AndreaFavero71/cubotino_pocket/stp/Structure_pocket.stp

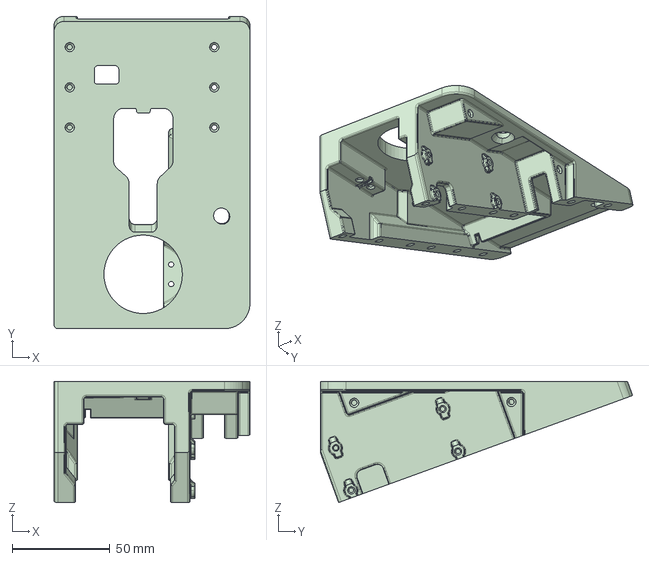
[picture p17: CAD file, 2024-02-11]
stp/Structure_pocket.stp
100.0 x 159.4 x 61.8 mm
