AndreaFavero71/cubotino_pocket/stp/PCB_cover_display_UsbC.stp

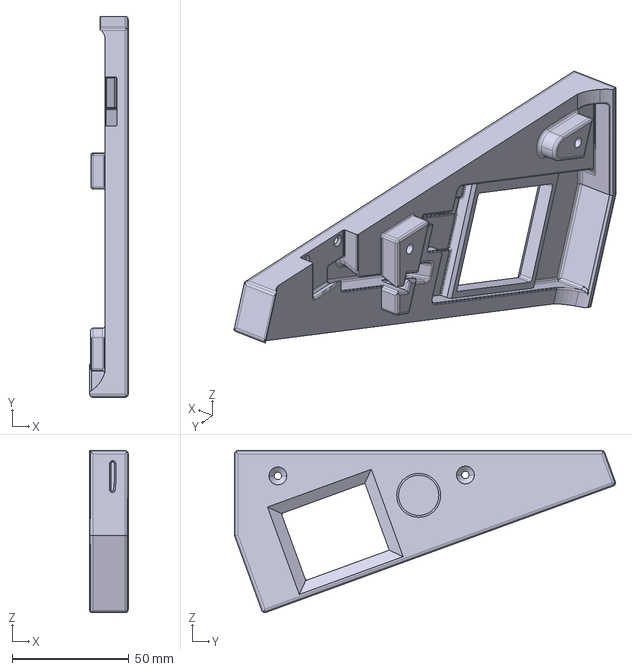
[picture p18: CAD file, 2024-02-11]
stp/PCB_cover_display_UsbC.stp
16.5 x 163.0 x 69.4 mm
