AndreaFavero71/cubotino_pocket/src/Cubotino_P.py

#!/usr/bin/python
# coding: utf-8

"""
#############################################################################################################
#  Andrea Favero, 29 March 2024
#
#  This code relates to CUBOTino 2x2x2 (Pocket), a very small and simple Rubik's cube solver robot 3D printed.
#  CUBOTino_P is the autonomous version of the CUBOTino robot series, for the 2x2x2 Rubik's cube.
#
#  Demo at https: https://youtu.be/wB4MwINGon0
#  Instructions: https://www.instructables.com/CUBOTino-Pocket-Optimal-Solver-Robot-for-Rubiks-Cu/
#
#  This is the core script, that interracts with a few other files.
#  Many functions of this code have been developed on 2021, for my first robot (https://youtu.be/oYRXe4NyJqs).
#
#  The cube status is detected via a camera system (PiCamera) and OpenCV .
#  Kociemba solver is used for the optimal solution (https://github.com/hkociemba/Rubiks2x2x2-OptimalSolver)
#  Credits to Mr. Kociemba for his great job, and helping me to modify the solver for optimal quarter turn.
#  Search for CUBOTino on www.instructables.com, to find more info about this robot family.
#
#  Developped on:
#  - Raspberry Pi Zero2W
#  - Raspberry Pi OS Bulleys, with desktop environment
#
#############################################################################################################
"""


# __version__ variable
version = '2.1 (29 March 2024)'


################  setting argparser for robot remote usage, and other settings  #################
import argparse

# argument parser object creation
parser = argparse.ArgumentParser(description='CLI arguments for Cubotino_P.py')

# --version argument is added to the parser
parser.add_argument("-v", "--version", help='Shows the script version.', action='version',
                    version=f'%(prog)s ver:{version}')

# --debug argument is added to the parser
parser.add_argument("-f", "--twosteps", action='store_true',
                    help="From Flip-Up to close_cover in 2 movements instead of 1")

# --debug argument is added to the parser
parser.add_argument("-d", "--debug", action='store_true',
                    help="Activates printout of settings, variables and info for debug purpose")

# --no_animation argument is added to the parser
parser.add_argument("--no_animation", action='store_true',
                    help="Deactivates the animation on display and screen")

# --cv_wow argument is added to the parser
parser.add_argument("--cv_wow", action='store_true',
                    help="Activates the cv_wow (image analysis steps) on screen")

# --F_deg argument is added to the parser
parser.add_argument("-F", "--F_deg", action='store_true',
                    help="CPU temperature in Fahrenheit degrees")

# --cycles argument is added to the parser
parser.add_argument("-c", "--cycles", type=int, 
                    help="Input the number of automated scrambling and solving cycles")

# --pause argument is added to the parser
parser.add_argument("-p", "--pause", type=int, 
                    help="Input the pause time, in secs, between automated cycles")

# --shutoff argument is added to the parser
parser.add_argument("-s", "--shutoff", action='store_true',
                    help="Shuts the RPI off, after the automated scrambling and solving cycles")

# --timer argument is added to the parser
parser.add_argument("-t", "--timer", action='store_true',
                    help="Timer is visualized after the scrambling function (max 1h)")

# --picamera_test argument is added to the parser
parser.add_argument("--picamera_test", action='store_true',
                    help="Visualizes PiCamera images for test purpose")

# --no_btn argument is added to the parser
parser.add_argument("--no_btn", action='store_true',
                    help="Starts the first solving cycles without using the touch button")

# --silent is added to the parser
parser.add_argument("--silent", action='store_true',
                    help="Deactivate servos, for 'quite' debug of non-servos related aspects")

# --slow_t is added to the parser
parser.add_argument("--slow_t", type=int,
                    help="Input additional resting (integer as tenth of secs) per each servo movement")

args = parser.parse_args()   # argument parsed assignement
# ###############################################################################################


import sys                                               # sys library is imported





def import_parameters(debug=False):
    """ Function to import parameters from a json file.
        It makes easier to list/document/change the variables that are expected to vary on each robot."""
    
    from Cubotino_P_settings_manager import settings as settings  # settings manager Class
    
    global frameless_cube, camera_width_res, camera_hight_res, s_mode
    global expo_shift, kl, x_l, x_r, y_u, y_b, w_f, w_s, square_ratio, rhombus_ratio
    global delta_area_limit, collage_w, marg_coef, cam_led_bright, cam_led_auto
    global detect_timeout, show_time, warn_time, quit_time, cover_self_close, vnc_delay, fcs_delay
    global built_by, built_by_x, built_by_fs

    try:                                                  # tentative
        sett = settings.get_settings()                    # settings are retrieved from the settings Class
        frameless_cube = sett['frameless_cube']           # cube frameless (with/without black frame around the facelets)
        expo_shift = sett['expo_shift']                   # camera exposure shift
        kl = sett['kl']                                   # coefficient for PiCamera stability acceptance (l= lower)
        x_l = sett['x_l']                                 # image crop on left (before warping)
        x_r = sett['x_r']                                 # image crop on right (before warping)
        y_u = sett['y_u']                                 # image crop on top (before warping)
        y_b = sett['y_b']                                 # image crop on bottom (before warping)
        w_f = sett['warp_fraction']                       # coeff for warping the image
        w_s = sett['warp_slicing']                        # coeff for cropping the bottom warped image
        square_ratio = sett['square_ratio']               # acceptance threshold for square sides difference
        rhombus_ratio = sett['rhombus_ratio']             # acceptance threshold for rhombus axes difference
        delta_area_limit = sett['delta_area_limit']       # acceptance threshold for facelet area dev from median
        collage_w = sett['collage_w']                     # image width for unfolded cube collage
        marg_coef = sett['marg_coef']                     # cropping margin arounf faces for immage collage
        cam_led_bright = sett['cam_led_bright']           # PWM level for the 3W led at Top_cover
        detect_timeout = sett['detect_timeout']           # timeout for cube status detection
        show_time = sett['show_time']                     # showing time of the unfolded cube image collage
        warn_time = sett['warn_time']                     # solve button pressing time before get a worning
        quit_time = sett['quit_time']                     # solve button pressing time before the quit process
        vnc_delay = sett['vnc_delay']                     # delay for cube moving to next face at scan (for VNC viewer)
        built_by = sett['built_by']                       # maker's name to add on the Cubotino logo
        built_by_x = sett['built_by_x']                   # x coordinate for maker's name on display
        built_by_fs = sett['built_by_fs']                 # font size for the maker's name on display
        fcs_delay = sett['fcs_delay']                     # delay in secs to switch to Fix Coordinates System for facelets position
        cover_self_close = sett['cover_self_close']       # cover_self_close parameter 
        
        if debug:                                         # case debug variable is set true
            fname = settings.get_settings_fname()         # settings filename is retrieved
            print('\nImporting settings from the text file:', fname)  # feedback is printed to the terminal
            for param, s in sett.items():                 # iteration over the settings dict
                print(f"{param}: {s}")                    # feedback is printed to the terminal
            print()                                       # prints an empty line
        
        return True, sett                                 # return True for loaded settings and the sett dictionary
    
    except:   # exception will be raised if json keys differs, or parameters cannot be converted to int/float
        print('Error at imported_parameters function in Cubotino_P.py')   # feedback is printed to the terminal                                  
        return False, ''                                  # return robot_init_status variable, that is False
    






def import_libraries():
    """ Import of the needed libraries.
        These librries are imported after those needed for the display management.
        Kociemba solver is tentatively imported considering three installation/copy methods."""
    
    global servo, rm, Popen, PIPE, camera, GPIO, median, dt, sv, cubie
    global np, math, time, cv2, os, pathlib
    
    # import custom libraries
    from Cubotino_P_settings_manager import settings as settings   # custom library managing the settings from<>to the settings files
    import Cubotino_P_servos as servo                     # custom library controlling Cubotino servos and led module
    import Cubotino_P_moves as rm                         # custom library, traslates the cuber solution string in robot movements string

    # import non-custom libraries
    from statistics import median                         # median is used as sanity check while evaluating facelets contours
    from subprocess import Popen, PIPE                    # module for interacting with some shell commands
    import os.path, pathlib                               # import libraries for file and folder management
    import RPi.GPIO as GPIO                               # import RPi GPIO library
    import datetime as dt                                 # mainly used as timestamp, like on data logging
    import numpy as np                                    # data array management
    import math                                           # math package
    import time                                           # time package
    import os                                             # os is imported to ensure the file presence check/make
    

    disp.show_on_display('LOADING', 'openCV', fs1=24, fs2=26)  # feedback is printed to the display
    print("Loading solver:")                              # feedback is printed to the terminal
    disp.set_backlight(1)                                 # display backlight is turned on, in case it wasn't
    import cv2                                            # computer vision package
    print(f'CV2 version: {cv2.__version__}')              # print to terminal the cv2 version
    disp.set_backlight(0)                                 # display backlight is turned off
    

    disp.show_on_display('LOADING', 'SOLVER', fs1=24, fs2=27)  # feedback is printed to the display
    print("Loading solver:")                              # feedback is printed to the terminal
    disp.set_backlight(1)                                 # display backlight is turned on, in case it wasn't

    # importing Kociemba solver
    solver_found = False                                  # boolean to track the import the copied solver in subfolder       
    folder = pathlib.Path().resolve()                     # active folder (should be home/pi/cubotino_pocket)  
    fname = os.path.join(folder,'solver2x2x2','solver.py') # active folder + Solver2x2x2 + solver name
    if os.path.exists(fname):                             # case the solver exists in 'Solver2x2x2' subfolder
        try:                                              # attempt
            import solver2x2x2.solver as sv               # import Kociemba solver copied in sub-folder
            import solver2x2x2.cubie as cubie             # import cubie Kociemba solver library part
            solver_found = True                           # boolean to track the  import the copied solver in subfolder
            if debug:                                     # case debug variable is set True            
                print('Found Kociemba solver in solver2x2x2 subfolder')  # feedback is printed to the terminal
        except:                                           # exception is raised if no library in folder or other issues
            solver_found = False                          # boolean to track the import the copied solver in subfolder
    else:
        solver_found = False                              # boolean to track the import the copied solver in subfolder
    
    if not solver_found:                                  # case no one solver has been imported
        print('\nNot found Kociemba solver')              # feedback is printed to the terminal
        disp.show_on_display('NO SOLVER', 'FOUND', fs1=19, fs2=28) # feedback is printed to the display
        time.sleep(5)                                     # delay to let user the time to read the display
        quit_func(quit_script=True)                       # script is quitted







def press_to_start():
    """ Print PRESS TO START to display, and waits until the touch button is pressed to escape the infinite loop"""
    
    global robot_idle
    
    choice = ''                                # variable to store the user choice (solve or scramble)
    robot_idle = True                          # robot is idling
    disp.set_backlight(1)                      # display backlight is turned on, in case it wasn't
    txt1 = 'PRESS TO'                          # text to print at first row
    txt2 = 'START'                             # text to print at second row
    fs_text2 = 32                              # font size at second row
    disp.show_on_display(txt1, txt2, fs2=fs_text2)   # request user to touch the button to start a cycle
    ref_time = time.time()                     # current time is assigned to ref_time variable
    cubotino_logo = False                      # boolean to alternate text with Cubotino logo on display
    display_time = 1                           # time (in sec) for each display page
    while True:                                # infinite loop
        if time.time() - ref_time >= display_time:   # time is checked
            if not cubotino_logo:              # case cubotino logo boolean is false  
                disp.show_cubotino()           # shows the Cubotino logo on the display, for delay time
                ref_time = time.time()         # current time is assigned to ref_time variable
                cubotino_logo = True           # cubotino logo boolean is set true                           
            else:                              # case cubotino logo boolean is false  
                disp.show_on_display(txt1, txt2, fs2=fs_text2)    # request user to touch the button to start a cycle
                ref_time = time.time()         # current time is assigned to ref_time variable
                cubotino_logo = False          # cubotino logo boolean is set false
            time.sleep(0.05)                   # little sleep time 
            
        if GPIO.input(touch_btn):              # case touch_button is 'pressed'
            servo.cam_led_On(cam_led_bright)   # led on top_cover is switched on as button feedback
            choice = solve_or_scramble()       # function for single/double touch (solve or scramble)
            return choice                      # choice is returned, breaking inner and outer while loop


##### addition for Maker Faire setup ##########
# it uses two inputs in logic AND to start the robot. These buttons don't do enything else (no scrambling, no time filtering)
        if GPIO.input(touch_btn1_faire) and GPIO.input(touch_btn2_faire):
            # case both the touch buttons on the faire setup are 'pressed'
            return 'solve'  # 'solve' is returned
###############################################







def solve_or_scramble():
    """ Sense for a single or double touches at the touch sensor, within a time limit.
        Returns 'solve' when single touch and 'scramble' when multiple touches.
        If the button is kept pressed longer, the robot can be restarted or shutted OFF."""
    
    global robot_idle, side
    
    choice = ''                               # variable to store the user choice (solve or scramble)
    state = False                             # boolean state to check flank is set false, 
    max_delay = 0.8                           # max time between touches, to decide if single or multi touches
    extra_time = 1.2                          # extra time to accept a single button press as intention to 'solve' a cube
    last_time = time.time()                   # variable holding the time of the last change to 'pressed' button
    pulse_count = 0                           # pulses counter is initially set to zero
    
    while robot_idle:                         # boolean robot_idle is used to sustain this loop
        new_state = GPIO.input(touch_btn)     # touch button status is assigned (it's ON when pressed)
        if new_state and not state:           # case the touch sensor changes from 'not pressed' to 'pressed'
            pulse_count += 1                  # pulse counter is incremented
            state = True                      # set the state to true
            last_time = time.time()           # updtaes the variable that hold
        elif not new_state:                   # case the touch sensor is 'not pressed'
            state = False                     # state is changed to false
        
        # case the elapsed time is bigger than max time and at least 1 pulse
        if time.time() > (last_time + max_delay) and pulse_count > 0:
            if GPIO.input(touch_btn):         # case button is still pressed
                if pulse_count == 1:          # case the button has been pressed only once
                    if time.time()< last_time + max_delay + extra_time: # case time is within the given extratime
                        servo.cam_led_Off()   # led OFF at Top_cover, to suggest the user to remove the finger
                        choice = 'solve'      # 'solve' is assigned to choice variable
                    else:                     # case elapsed time is more than extra_time
                        servo.cam_led_Off()   # led OFF at Top_cover
                        break                 # while loop is interrupted
                elif pulse_count > 1:         # case the button has been pressed multiple times
                    servo.cam_led_Off()       # led OFF at Top_cover
                    break                     # while loop is interrupted

            elif not GPIO.input(touch_btn):   # touch button is NOT pressed
                if pulse_count == 1:          # case pulses equal one, and button not 'pressed'
                    choice = 'solve'          # 'solve' is assigned to choice variable
                elif pulse_count >= 2:        # case pulses are two or more,  and button not 'pressed'
                    servo.cam_led_Off()       # led OFF at Top_cover when scrambling is chosen
                    choice = 'scramble'       # 'scramble' is assigned to choice variable
                else:                         # other cases (button kept pressed long without a release within maxtime)
                    pulse_count = 0           # pulse counter is reset to zero
                    choice = ''               # empty string is assigned to choice variable
                return choice                 # choice is returned
    
    servo.cam_led_Off()    # led OFF at Top_cover when scrambling is chosen
    robot_idle = False     # robot_idle is set false
    stop_or_quit()         # stop or quit function is called, when the while loop is interrupted
    choice = ''            # empty string is assigned to choice variable
    return choice          # choice is returned







def check_screen_presence():
    """ Checks if a display is connected, eventually via VNC; This is not the little display (SPI) ...."""
    
    import os
    
    if 'DISPLAY' in os.environ:                # case the environment variable DISPLAY is set to 1 (there is a display)
        return True                            # function returns true, meaning there is a screen connected
    else:                                      # case the environment variable DISPLAY is set to 0 (there is NOT a display)
        return False                           # function returns false, meaning there is NOT a screen connected







def get_os_version():
    """Returns the Raspberry Pi OS (in digits)."""
    os_version = 0
    with open('/etc/os-release', 'r') as file:
        for row in file:
            if "VERSION_ID" in row:
                os_version = int(''.join(x for x in row if x.isdigit()))
                return os_version
    return os_version







def set_camera(expo_shift=0):
    """ Set the camera and its resolution.
        Different libraries will be used depending on OS version (picamera on OS 10, picamera2 on OS 11)"""
  
    os_version = get_os_version()
    
    if os_version >0 and os_version <= 10:
        from Cubotino_P_camera_os10 import camera
        width = camera.get_width()
        height = camera.get_height()
        
        # case cube side is zero, no request to stop the robot and not automated cycles
        if side == 0 and not robot_stop and cycles_num == 0 and not picamera_test:
            camera.printout()
        
    elif os_version >= 11:
        from Cubotino_P_camera_os11 import camera
        width = camera.get_width()
        height = camera.get_height()
        time.sleep(1)
        camera.set_exposure_shift(expo_shift)
    
    else:
        print("Raspberry Pi OS version not recognized")
    
    return camera, width, height







def robot_camera_setting(debug, os_version, camera):
    """ According to PiCamera documentation it is required a couple of seconds to warmup the camera.
    If the robot start-button is pressed right after placing the cube, the camera has to update the gains previously set,
    that means from when the camera was pointing the black cube support; this can take up to 20 secs to get all
    the gains stable (awb gains are rather slow to update).
    Much different is when the cube is on the cube support for few secs when the button is pressed.
    To properly cover all the possible situations, this fuction releases the camera warm-up phase only after
    all the gains are stable. This function returns the camera parameters once within absolute variation < 5% from
    the average of 'pts' points."""
    
    stable_camera = False           # flag to trak whether the camera gets stable within the timeout
    
    ku = 2-kl                       # Upper koefficient to define acceptance bandwidth (105%)
    
    if os_version <= 10:            # case the OS is Buster or older
        t_max = 5                   # timeout to quit this function and deliver the latest camera parameters
        if debug:                   # case debug variable is set True
            pts = 8                 # consecutive datapoints to analyse if parameters within acceptable range
        else:                       # case debug variable is set False
            pts = 10                # consecutive datapoints to analyse if parameters within acceptable range
        
    elif os_version >= 11:          # case the OS is Bullseye or newer
        t_max = 3                   # timeout to quit this function and deliver the latest camera parameter
        if debug:                   # case debug variable is set True
            pts = 9                 # consecutive datapoints to analyse if parameters within acceptable range
        else:                       # case debug variable is set False
            pts = 11                # consecutive datapoints to analyse if parameters within acceptable range
    
    if Rpi_ZeroW:                   # case a ZeroW board is used
        t_max = 3*t_max             # max time for camera setting is increased
    
    a_gain_list=[]                  # list to store the Picamera analog gain, during pre-scan period
    d_gain_list=[]                  # list to store the Picamera digital gain, during pre-scan period
    awb_blue_list=[]                # list to store the Picamera AWB gain, for blue, during pre-scan period
    awb_red_list=[]                 # list to store the Picamera AWB gain, for red, during pre-scan period
    exp_list=[]                     # list to store the Picamera exposure time, during pre-scan period
    PiCamera_param=()               # empty tuple is assigned to PiCamera_param variable
    
    if screen and not robot_stop:                      # case screen variable is set True
        if fixWindPos:                                 # case the fixWindPos variable is chosen
            cv2.namedWindow('cube')                    # create the cube window
            cv2.moveWindow('cube', 0,0)                # move the window to (0,0)

    t_start = time.time()                              # time reference
    while time.time()-t_start<t_max:                   # timeout for camera stabilization
        if screen and not robot_stop:                  # case screen variable is set True
            frame, w, h = read_camera()                # camera reading, not necessary but nice to show
            cv2.imshow('cube', frame)                  # shows the frame 
            cv2.waitKey(1)                             # tot refresh time of 1ms (in reality much more)
        else:                                          # case screen variable is set False
            time.sleep(0.11)                           # similar time when there is no camera reading and plot to screen
        
        if os_version <= 10:                           # case the flashed OS is 10 (Buster) or older
            metadata = camera.get_data()               # camera is inquire
        elif os_version >= 11:                         # case the flashed OS is 11 (Bullseye) or newer
            metadata = camera.get_metadata()           # camera is inquired
        
        a_gain = metadata["AnalogueGain"]              # analog gain from metadata is assigned to the variable
        d_gain = metadata["DigitalGain"]               # digital gain from metadata is assigned to the variable
        awb_gains = metadata["ColourGains"]            # AWB gains from metadata is assigned to the variable
        exposure = metadata["ExposureTime"]            # exposure time from metadata is assigned to the variable        
        
        a_gain_list.append(float(a_gain))              # analog gain is appended to a list
        d_gain_list.append(float(d_gain))              # digital gain is appended to a list
        awb_blue_list.append(float(awb_gains[0]))      # awb blue part gain is appended to a list
        awb_red_list.append(float(awb_gains[1]))       # awb blue part gain is appended to a list
        exp_list.append(exposure)                      # exposure time (micro secs) is appended to a list

        a_check=False                                  # a flag is negatively set for analog gain (being stable...)
        d_check=False                                  # a flag is negatively set for digital gain (being stable...)
        awb_blue_check=False                           # a flag is negatively set for awb blue gain (being stable...)
        awb_red_check=False                            # a flag is negatively set for awb red gain (being stable...)
        exp_check=False                                # a flag is negatively set for the exposure time (being stable...)

        if len(a_gain_list) > pts:                     # requested a minimum amount of datapoints
            check = a_gain_list[-1]/(sum(a_gain_list[-pts:])/pts)  # last analog gain value is compared to the average of last pts points
            if check > kl and check < ku:              # if comparison within acceptance boundaries
                a_check=True                           # flag is positively set for this gain             
        
            check = awb_blue_list[-1]/(sum(awb_blue_list[-pts:])/pts) # last awb_blue gain is compared to the average of last pts points
            if check > kl and check < ku:              # if comparison within acceptance boundaries
                awb_blue_check=True                    # flag is positively set for this gain    
                
            check = awb_red_list[-1]/(sum(awb_red_list[-pts:])/pts) # last awb_red gain is compared to the average of last pts points
            if check > kl and check < ku:              # if comparison within acceptance boundarie
                awb_red_check=True                     # flag is positively set for this gain
            
            check = exp_list[-1]/(sum(exp_list[-pts:])/pts)  # last exposure time is compared to the average of last pts points
            if check > kl and check < ku:              # if comparison within acceptance boundarie
                exp_check=True                         # flag is positively set for the exposure time                
     
            if a_check and awb_blue_check and awb_red_check and exp_check: # if all gains are stable
                stable_camera = True
                break                                  # camera warmup while loop break
     
    if len(a_gain_list)==0:                            # case a_gain_list (the first list of camera setting) is empty
        print("The camera takes very long time to stabilize")  # feedback is printed to terminal
        print("The script is ended")                   # feedback is printed to terminal
        quit_func(quit_script=True)                    # script is quitted
    else:                                              # case the first list (a_gain_list) is not empty
        a_gain_value = a_gain_list[-1]                 # last a_gain list value is assigned
        d_gain_value = d_gain_list[-1]                 # last d_gain list value is assigned
        awb_gains = (awb_blue_list[-1], awb_red_list[-1])  # last awb_gains list tuple is assigned
        exposure = exp_list[-1]                        # last exposure list value is assigned
    
    # latest PiCamera settings, in auto mode, are assigned to a tuple
    PiCamera_param=(a_gain_value, d_gain_value, awb_gains, exposure, stable_camera)  
    
    t_stable = round(time.time()-t_start,1)            # time to get the camera stable on this cube face
    
    if debug:                                          # case debug is set True
        print('\nPiCamera warmup function:')           # feedback is printed to the terminal
        print('analog_gain_list',a_gain_list)          # feedback is printed to the terminal
        print('digital_gain_list',d_gain_list)         # feedback is printed to the terminal
        print('awb_blue_list',awb_blue_list)           # feedback is printed to the terminal
        print('awb_red_list',awb_red_list)             # feedback is printed to the terminal
        print('camera exp_list', exp_list)             # feedback is printed to the terminal
        print('datapoints:', len(exp_list))            # feedback is printed to the terminal
        print(f'PiCamera: AWB and Exposure being stable in {t_stable} secs')  # feedback is printed to the terminal
    
    return PiCamera_param                              # tuple with the camera stable parameter is returned







def robot_consistent_camera_images(debug, os_version, camera, start_time):
    """ Picamera is left in set in Auto mode for Exposure and AWB gains, while presenting 4 cube faces.
    These parameters are retrieved from PiCamera after showing each of these first 4 cube faces.
    Picamera is then set to Manual mode by setting the average exposure time and average AWB to the camera.
    This approach prevents the PiCamera to keep adjusting the AWB and Exposure while reading the different cube faces.
    The average values set to the camera mitigates large differences at the cube, i.e. when the cube is already solved."""
    
    if robot_stop:            # case the robot has been requested to stop
        return                # function is terminated
    
    disp.show_on_display('SETTING', 'CAMERA', fs1=23, fs2=21)    # feedback is printed to the display
    
    
    if os_version <= 10:
        awb_mode = 0          # this is the AUTO mode fro the AWB, and it works well with Cubotino
    
    elif os_version >= 11:
        # AWB mode (AutoWitheBalance) to use when the camera is set to automati mode
        # AwbMode: 0=Auto - any illumant, 1=Tungsten - tungsten lighting, 2=Fluorescent - fluorescent lighting
        # 3=Indoor - indoor illumination, 4=Daylight - daylight illumination, 5=Cloudy - cloudy illumination
        awb_mode = 3          # this is the  mode that seems to work better in Cubotino
    
    camera.set_auto(debug, awb_mode, expo_shift)        # camera is set to automatic mode, by also passing the chosen AWB mode
    
    if debug:                                           # case debug variable is set True
        print("\nCamera settings (in Auto mode):")      # feedback is printed to the terminal
        print('\nPiCamera: Reading the stable camera parameters on four cube sides')  # feedback is printed to the terminal

    a_gain_list=[]                                      # list to store the Picamera analog gain, during pre-scan period
    d_gain_list=[]                                      # list to store the Picamera digital gain, during pre-scan period
    awb_blue_list=[]                                    # list to store the Picamera AWB gain, for blue, during pre-scan period
    awb_red_list=[]                                     # list to store the Picamera AWB gain, for red, during pre-scan period
    exp_list=[]                                         # list to store the Picamera exposure time, during pre-scan period
    stable_camera_list=[]                               # list to store the Picamera stability reach within timeout

    # PiCamera is inquired on 4 cube sides reachable via a simple cube flip, to later fix an average parameters
    for i in (1,2,3,4):                                 # iterate over 4 faces reachable via a single cube flip    
        if i > 1:                                       # case i (face) is not the first
            robot_to_cube_side(1,cam_led_bright)        # flipping the cube, to reach the next side 

        PiCamera_param = robot_camera_setting(debug, os_version, camera)  # camera parameter are returned
        a_gain_list.append(PiCamera_param[0])           # analog gain is added to a_gain_list
        d_gain_list.append(PiCamera_param[1])           # digital gain is added to d_gain_list
        awb_blue_list.append(PiCamera_param[2][0])      # awb blue is added to awb_blue_list
        awb_red_list.append(PiCamera_param[2][1])       # awb red is added to awb_red_list
        exp_list.append(PiCamera_param[3])              # exposure time is added to exp_list
        stable_camera_list.append(PiCamera_param[4])    # boolean stable_camera is added to stable_camera_list
        
        if debug:                                       # case debug variable is set True
            print(f"\nCamera settings (in Auto mode) at face {i}:")  # feedback is printed to the terminal
            print(PiCamera_param)                       # feedback is printed to the terminal
            print()                                     # print an empty line
            if i == 4:                                  # case i (face) equals four
                print("\n"*3)                           # prints 3 empty lines
    
    # setting the camera in manual mode, for consistent images when scanning
    a_gain = float(sum(a_gain_list)/len(a_gain_list))   # average a_gain is calculated and assigned
    d_gain = float(sum(d_gain_list)/len(d_gain_list))   # average d_gain is calculated and assigned
    awb_gains = (float(sum(awb_blue_list)/len(awb_blue_list)), float(sum(awb_red_list)/len(awb_red_list)))  # average awb_gains is calculated and assigned
    shutter_time = int(sum(exp_list)/len(exp_list))     # average exposure time of UBDF faces
    
    camera.set_gains(debug, a_gain, d_gain, awb_gains)  # sets the gains to the PiCamera, for consisent images
    camera.set_exposure(shutter_time)                   # sets the shutter time to the PiCamera, for consistent images
    
    t_ref = time.time()                                 # current time is assigned to a reference variable
    while time.time()-t_ref < 2:                        # while loop for max 2 seconds
        exposure = camera.get_exposure()                # read picamera exposure time (microsec)
        if abs(exposure-shutter_time) < 0.10*shutter_time:  # case the camera shutter time deviates less than 10% from target shutter_time
            break                                       # while loop is interrupted       
    
    if screen:                                          # case there is a screen connected
        print(f'Camera setting: Fixed gains and shutter time for cube  scanning, in {round(time.time()-start_time,1)} secs')# feedback is printed to the terminal
    
    if debug:                                           # case debug variable is set True
        print('\n\nExposure time on UBDF faces : ', exp_list)  # feedback is printed to the terminal
        print('Average exposure time: ', int(sum(exp_list)/len(exp_list)), 'micro secs') # feedback is printed to the terminal
        print('Shutter_time set by PiCamera: ', camera.get_exposure(), ' micro secs')  # feedback is printed to the terminal
        print('Camera stable within timeout', stable_camera_list)   # feedback is printed to the terminal
        print('\nPiCamera parameters, for consistent images, are set to:')  # feedback is printed to the terminal
        print('Analog_gain_list',a_gain_list)           # feedback is printed to the terminal
        print('Digital_gain_list',d_gain_list)          # feedback is printed to the terminal
        print('Awb_blue_list',awb_blue_list)            # feedback is printed to the terminal
        print('Awb_red_list',awb_red_list)              # feedback is printed to the terminal
        print("\n"*4)                                   # prints four empty lines

    disp.clean_display()                                # cleans the display
    robot_to_cube_side(1,cam_led_bright)                # flipping the cube, to reach the 1st face for the scanning process







def read_camera():
    """ Returns the camera reading, and dimensions."""
    
    global previous_time
    
    frame = camera.get_frame()                                    # single frame array request to camera Class
    width = camera.get_width()                                    # camera width request to camera Class
    height = camera.get_height()                                  # camera height request to camera Class
    
    if len(frame)==0:                                             # case the frame is empty
        print('camera frame not available')                       # feedback is print to the terminal
    
    else:                                                         # case the frame is not empty
        if not picamera_test:                                     # case picamera_test is false
            frame, w, h = frame_cropping(frame, width, height, x_l, x_r, y_u, y_b)  # frame is cropped in order to limit the image area to analyze
            frame, w, h = warp_image(frame, w, h, w_f, w_s)       # frame is warped to have a top like view toward the top cube face
            scale = 0.75 if cv_wow else 0.8                       # scaling factor according to cv_wow i 
            frame, w, h = frame_resize(frame, w, h, scale=scale)  # frame is resized (to smaller size), to gain some speed
        
        elif picamera_test:                                       # case picamera_test is True (also when servos_GUI script is used):
            w = width                                             # widht is assigned to w
            h = height                                            # height is assigned to h
        
        return frame, w, h







def frame_cropping(frame, width, height, x_l, x_r, y_u, y_b):
    """Frame cropping, to prevent reading the back cube side and to increase overal speed.
    Due to short camera distance from the cube, all the PiCamera sensor area is used,
    therefore pixels reduction is beneficial ro reduce overall memory load.
    For proper setting of these parameters, it is convenient to temporary skip the frame_warping:
    uncomment first row at frame_warping function."""
    
#     uncomment below row (return frame, width, height) to prevent the image cropping
#     this is useful for initial camera positioning (angle) on the top_cover
#     return frame, width, height
    
    frame = frame[y_u: height-y_b , x_l: width-x_r]   # frame is sliced
    w = width - x_l - x_r                             # sliced frame width
    h = height - y_u - y_b                            # sliced frame height
    
    return frame, w, h







def warp_image(frame, w, h, w_f, w_s):
    """ Warp the image to remove perspective and simulate a top like view.
    This because PiCamera is at an angle with reference to the top cube face.
    This allows to analyse the facelets contours (square like, area, etc) in a more precise way.
    This also allows a much nicer cube faces collage."""
    
#     NOTE: uncomment below row to remove the image warping, useful for initial setting the camera frame cropping (frame_cropping)
#     return frame, w, h
    
    if cv_wow:                        # case the cv image analysis plot is set true
        global pre_warp, after_warp   # global variable for the frame content, before and after warping
        pre_warp = frame              # frame is assigned to the pre_warp variable
        ww = w                        # frame width before warping is assigned to a local variable
        hh = h                        # frame height before warping is assigned to a local variable
    
    grid_vertices = np.float32([[0,0], [h,0], [h,w], [0,w]])  # original frame vertices

    d_x = int(w/w_f)            # pixels to 'remove' on top left and top righ sides of frame, to warp the image
    straight = 1+d_x/h          # corrects the cube face deformation 

    warped_vertices = np.float32([[d_x,0], [h,0], [int(straight*h),w], [-d_x, w]])  # frame coordinates for the transformation matrix
    matrix = cv2.getPerspectiveTransform(warped_vertices, grid_vertices)            # compute perspective matrix

    # do perspective transformation, by adding black pixels where needed
    frame = cv2.warpPerspective(frame, matrix, (max(w,h), max(w,h)), cv2.INTER_LINEAR, cv2.BORDER_CONSTANT, borderValue=(0,0,0))
    
    frame = frame[: -d_x, :-int(d_x/w_s)]   # frame slicing to remove part of the added (black) pixels on the right frame side 
    h, w = frame.shape[:2]                  # new frame height and width
    
    if cv_wow:                                           # case the cv image analysis plot is set true
        pre_warp, _, _ = frame_resize(pre_warp, ww, hh)  # re-sized frame is assigned to the pre_warp global variable
        after_warp, _, _ = frame_resize(frame, w, h)     # re-sized frame is assigned to the after_warp global variable
    
    return frame, w, h







def frame_resize(frame_w, ww, hh, scale=0.8):        
    """ Re-sizes the image after the cropping and warping steps, by a scaling factor.
    This is useful to lower the amount of handled data for the facelects and color detection."""
    
    ww = int(ww * scale)                  # new frame width
    hh = int(hh * scale)                  # new frame height
    
    if Rpi_ZeroW:                         # case Rpi_ZeroW is True (armv6 processor)
        interp_method = cv2.INTER_LINEAR  # bilinear interpolation method (prevents crashing with armv6 processor))
    else:                                 # case Rpi_ZeroW is False (not an armv6 processor)
        interp_method = cv2.INTER_AREA    # interpolation method resamples using pizel area relation

    frame_s = cv2.resize(frame_w, (ww, hh), interpolation = interp_method)  # resized frame
    return frame_s, ww, hh







def edge_analysis(frame, w, h):
    """ Image analysis that returns a black & white image, based on the colors borders.
        Different analysis for cube with /withouth the black frame around the facelets."""
    
    if cv_wow and screen:                                    # case screen and cv_wow variables are set true on __main__
        global gray, blurred, canny, dilated, eroded         # images are set as global variable

    gray = cv2.cvtColor(frame, cv2.COLOR_BGR2GRAY)           # from BGR color space to gray scale
    
    if frameless_cube == 'false':                            # case the cube has black frame around the facelets
        blurred = cv2.GaussianBlur(gray, (5, 5), 0)          # low pass gaussian filter, with a 5x5 gaussian filter
        canny = cv2.Canny(blurred, 10, 30)                   # single pixel edges, with intensity gradient range 10 to 30
        kernel = np.ones((5,5), np.uint8)                    # kernel of 5x5 pixels for the dilate transformation
        dilated = cv2.dilate(canny, kernel, iterations = 4)  # higher "iterations" is overall faster
        kernel = np.ones((3,3), np.uint8)                    # smaller kernel is used for the erosion
        eroded = cv2.erode(dilated, kernel, iterations = 2)  # smaller "iterations" keeps the contour apart from the edges
    
    elif frameless_cube == 'true':                           # case the cube is a frameless cube
        blurred = cv2.bilateralFilter(gray, 3, 80, 80)       # low pass bilateral filter, to de-noise while safegarding edges
        canny = cv2.Canny(blurred, 4, 25)                    # single pixel edges, with intensity gradient range 4 to 25
        kernel = np.ones((7,7), np.uint8)                    # kernel of 7x7 pixels for the dilate transformation
        dilated = cv2.dilate(canny, kernel, iterations = 4)  # higher "iterations" is overall faster
        kernel = np.ones((5,5), np.uint8)                    # smaller kernel is used for the erosion
        eroded = cv2.erode(dilated, kernel, iterations = 1)  # smaller "iterations" keeps the contour apart from the edges
    
    # note: when frameless_cube == 'auto' the cube detection takes slightly longer
    elif frameless_cube == 'auto':                           # case for cubes with and without the black frame around the facelets
        blurred = cv2.GaussianBlur(gray, (5, 5), 0)          # low pass gaussian filter, with a 5x5 gaussian filter
        canny_01 = cv2.Canny(blurred, 10, 30)                # single pixel edges, with intensity gradient range 10 to 30
        blurred = cv2.bilateralFilter(gray,4, 200, 200)      # low pass bilateral filter, to de-noise while safegarding edges
        canny_02 = cv2.Canny(blurred, 4, 25)                 # single pixel edges, with intensity gradient range 4 to 25
        canny = cv2.bitwise_or(canny_01, canny_02, mask = None) # canny image, by (OR) combining those generated with parameters with and without frames
        kernel = np.ones((7,7), np.uint8)                    # kernel of 7x7 pixels for the dilate transformation
        dilated = cv2.dilate(canny, kernel, iterations = 3)  # higher "iterations" is overall faster
        kernel = np.ones((3,3), np.uint8)                    # smaller kernel is used for the erosion
        eroded = cv2.erode(dilated, kernel, iterations = 2)  # smaller "iterations" keeps the contour apart from the edges
    
############ visual check edge detection #############
#     cv2.imshow("Gray", gray)           # gray is shown, on a window called Gray
#     cv2.imshow("blurred", blurred)     # blurred is shown, on a window called Blurred
#     cv2.imshow("Canny", canny)         # canny is shown, on a window called Canny
#     cv2.imshow("Dilated", dilated)     # dilated is shown, on a window called Dilated
#     cv2.imshow("Eroded", eroded)       # eroded is shown, on a window called Eroded
######################################################
    
    return eroded, w, h







def show_cv_wow(cube, time=2000):
    """ shows how the image from the camera is altered to detect the facelets.
        Also possible to set a boolean to save those images."""
    
    gap_w = 80       # horizontal gap (width) for all windows from 'Pre_warp' window
    gap_h = 100      # vertical gap (height), above first row of images and between the two rows of windows
    
    # note: for precise window position, after windows name at cv2.namedWindow, the parameter cv2.WINDOW_NORMAL  
    # should be used instead of the cv2.WINDOW_RESIZE (default), but image quality on screen changes too much....
    cv2.namedWindow('Pre_warp')                      # create the Pre_warp window
    cv2.moveWindow('Pre_warp', w, gap_h)             # move the Pre_warp window to coordinate
    cv2.namedWindow('After_warp')                    # create the Frame window
    cv2.moveWindow('After_warp', 2*w+gap_w, gap_h)   # move the Frame window to coordinate
    cv2.namedWindow('Gray')                          # create the Gray window
    cv2.moveWindow('Gray', 3*w+gap_w, gap_h)         # move the Gray window to coordinate
    cv2.namedWindow('blurred')                       # create the Blurred window
    cv2.moveWindow('blurred', 4*w+gap_w, gap_h)      # move the Blurred window to coordinate
    cv2.namedWindow('Canny')                         # create the Canny window
    cv2.moveWindow('Canny', w+gap_w, h+2*gap_h)      # move the Canny window to coordinate
    cv2.namedWindow('Dilated')                       # create the Dilated window
    cv2.moveWindow('Dilated', 2*w+gap_w, h+2*gap_h)  # move the Dilated window to coordinate
    cv2.namedWindow('Eroded')                        # create the Eroded window
    cv2.moveWindow('Eroded', 3*w+gap_w, h+2*gap_h)   # move the Eroded window to coordinate
    cv2.namedWindow('Cube')                          # create the Cube window
    cv2.moveWindow('Cube', 4*w+gap_w, h+2*gap_h)     # move the Cube window to coordinate
    
    cv2.imshow("Pre_warp", pre_warp)                 # pre-warp is shown, on a window called Pre_warp
    cv2.imshow("After_warp", after_warp)             # after_warp is shown, on a window called After_warp
    cv2.imshow("Gray", gray)                         # gray is shown, on a window called Gray
    cv2.imshow("blurred", blurred)                   # blurred is shown, on a window called Blurred
    cv2.imshow("Canny", canny)                       # canny is shown, on a window called Canny
    cv2.imshow("Dilated", dilated)                   # dilated is shown, on a window called Dilated
    cv2.imshow("Eroded", eroded)                     # eroded is shown, on a window called Eroded
    cv2.imshow("Cube", cube)                         # cube is shown, on a window called Cube
    
    if side == 1:                   # case the first cube side is under analysis 
        cv2.waitKey(time + 4000)    # all the openCV windows are showed, with an extra time on first cube side
    else:                           # case the cube side under analysis is not the first side
        cv2.waitKey(time)           # all the openCV windows are showed
    
    save_images = False                                         # boolean to enable/disable saving cv_wow images
    folder = pathlib.Path().resolve()                           # active folder (should be home/pi/cubotino_pocket)  
    if save_images:                                             # case the save_image is True
        folder = os.path.join(folder,'cv_wow_pictures')         # folder to store the cv_wow pictures
        if not os.path.exists(folder):                          # if case the folder does not exist
            os.makedirs(folder)                                 # folder is made if it doesn't exist
        datetime = dt.datetime.now().strftime('%Y%m%d_%H%M%S')  # date_time variable is assigned, for file name
        for i, image in enumerate(('Pre_warp', 'After_warp', 'Gray', 'Blurred', 'Canny', 'Dilated', 'Eroded', 'Cube')):
            if side == 1 and i == 0:                                       # case for first image to save
                print('\n\n##########################################')    # feedback is printed to the terminal
                print('###   saving 48 cv_wow pictures  !!!  ####')        # feedback is printed to the terminal
                print('##########################################\n\n')    # feedback is printed to the terminal
            fname = datetime + '_Side'+ str(side) + '_' + str(i) + '_'+ image + '.png'  # filename constructor
            fname = os.path.join(folder, fname)         # folder+filename for the cube data
            if image == 'Pre_warp':                     # case the image equals to Pre_warp
                cv2.imwrite(fname, pre_warp)            # pre_warp image is saved
            elif image == 'After_warp':                 # case the image equals to Frame
                cv2.imwrite(fname, after_warp)          # frameimage is saved
            elif image == 'Gray':                       # case the image equals to Gray
                cv2.imwrite(fname, gray)                # gray image is saved
            elif image == 'Blurred':                    # case the image equals to Blurred
                cv2.imwrite(fname, blurred)             # blurred image is saved
            elif image == 'Canny':                      # case the image equals to Canny
                cv2.imwrite(fname, canny)               # canny image is saved
            elif image == 'Dilated':                    # case the image equals to Dilated
                cv2.imwrite(fname, dilated)             # dilated image is saved
            elif image == 'Eroded':                     # case the image equals to Eroded
                cv2.imwrite(fname, eroded)              # eroded image is saved
            elif image == 'Cube':                       # case the image equals to Cube
                cv2.imwrite(fname, cube)                # cube image is saved
            else:                                       # case the does not match proposed strings
                print('Error in image list')            # feedback is printed to the terminal







def square_check(data):  
    """Sanity check if a contour has a square like shape; Argument is a contour.
    Calculates quadrilateral's edge delta lenght: [(max edge - min edge)/average of sides length]
    Calculates the ratio between the 2 diagonals (rhonbus axes): min diagonal / max diagonal
    These parameter are later used to verify if the contour can be considered like a square.
    A perfect square will have edge_delta==0 and axes_delta==1."""
    
    edges=[]                    # list of the 4 edges of the quadrilateral
    axes=[]                     # List of axes of symmetry length of the rhombus
    for i in range(len(data)):  # iteration over the contour vertices 
        j = i + 1               # following vertex
        if i==3:                # case the current iteration is on vertex 
            j=0                 # following vertex is set as the first one
        edges.append(math.sqrt((data[j][0]-data[i][0])**2 + (data[j][1]-data[i][1])**2))  # list of the 4 edge's length
        edge_delta = (max(edges)-min(edges))*4/sum(edges)                                 # max side delta over the mean
    
    for i in range(2):          # iteration over 2 (diagonals)
        j = i + 2               # following vertices is the after the next 
        axes.append(math.sqrt((data[j][0]-data[i][0])**2 + (data[j][1]-data[i][1])**2))  # list of the 2 rhobus axes
        axes_delta = min(axes)/max(axes)    # axes delta is the division of the smallest over the largest
    
    return edge_delta, axes_delta







def distance_deviation(data, delta=0.3):
    """ Checks whether the distances between the 4 contours centers are within a pre-defined deviation from the median
    This is a sanity check if all the 4 facelets are compatible with a 2x2 square array shape.
    Aim of this funtion is to exclude contours generated outside the cube, on eventual square like shapes
    detected by the camera at the cube background.
    The approach checks the 2 horizontal distances from the contours center, and the 2 vertical ones.
    Considering the cube can have a certain tilting angle (inclination), Pitagora theorem is used.
    Function returns a list with the index of the countours (exceding the threshold) to be removed from the
    list of contours considered being potential facelets.
    ---------
    | 0 | 1 |
    ---------
    | 2 | 3 | 
    ---------  
    """
    
    d_to_exclude = []        # list of the contour index to be removed, due to excess of distance deviation
    distance_list = []       # list of the horizontal and vertical distance, of each contour from the median
    
    points_h=[1,3]           # coordinates, defining a segment with a previous coordinate,for 2 'horizontal' distances
    for i in points_h:       # iteration over the 6 coordinates
        j=i-1                # the other coordinate used for the segment length
        # horizontal distance between the contours centers
        dist=math.sqrt((data[i]['cx']-data[j]['cx'])**2 + (data[i]['cy']-data[j]['cy'])**2)
        distance_list.append(dist)  # list with horizontal distance between the contours centers

    points_v=[2,3]           # coordinates, defining a segment with a previous coordinate,for 2 'vertical' distances
    for i in points_v:       # iteration over the 6 coordinates
        k=i-2                # the other coordinate used for the segment length
        # vertical distance between the contours centers
        dist=math.sqrt((data[i]['cx']-data[k]['cx'])**2 + (data[i]['cy']-data[k]['cy'])**2)
        distance_list.append(dist)  # list with horizontal and vertical distance between the contours centers

    dist_median = median(distance_list)                               # median value for horiz and vert distances
    for i in range(len(distance_list)):                               # iteration over the list with the (expected 4) distances
        delta_dist = (distance_list[i]-dist_median)/dist_median       # distance deviation
        if delta_dist > delta:                                        # filter if deviation > threshold
            d_to_exclude.append(i) # list with contours index to exlude, due excess on deviation from median
            if debug:
                print(f"removing contour {i} as its centers dists more than {delta} from median distance between contours")
    
    return d_to_exclude







def read_facelets(frame, w, h):
    """ Function that uses cv2 to retrieve contours, from an image (called frame in this case).
    Contours are searched on the 'eroded edges' frame copy.

    Notes on 'cv2 find contours'
    Contour's tree is used (cv2.RETR_TREE), to identify children contours (contours within other contrours)
    Approximation (v2.CHAIN_APPROX_SIMPLE) reduces the amount of pixel down to only vertes."""
    
    global prev_side
 
    if side!=prev_side:                           # case the current side differs from the previous side
        if debug:                                 # case debug variable is set True
            print()                               # print an empty line to the terminal
        print(f'Reading side {sides[side]}')      # feedback is printed to the terminal
        prev_side=side                            # current side is assigned to previous side variable

    image, w, h = edge_analysis(frame, w, h)      # image edges analysis is applied to the frame
    (contours, hierarchy) = cv2.findContours(image, cv2.RETR_TREE, cv2.CHAIN_APPROX_SIMPLE)  # contours are searched on the image
    
    return (contours, hierarchy)                  # contours are returned







def get_approx_contours(component):
    """ Function that simplifies contours (from: https://docs.opencv.org/4.5.3/dd/d49/tutorial_py_contour_features.html).
    Argument is a contour, having at least 4 vertex (contours with less than 4 vertex were previously filtered out)
    Returns approximated contours, having 4 vertex.""" 
    
    contour = component[0]
    hierarchy = component[1][2]
    peri = cv2.arcLength(contour, True)
    contour_convex = cv2.convexHull(contour, False)
    contour = cv2.approxPolyDP(contour_convex, 0.1*peri, True)
    
    return contour, hierarchy, len(contour)







def get_facelets(facelets, frame, contour, hierarchy):
    """ Contours are analyzed in order to detect the cube's facelets; Argument are simplified contours.
    The function returns contours having square characteristics.
    
    [parameter to be square like: Area within limits, limited egde lenght deviation, limited diagonals lenght deviation
    (to prevent rhonbus), limited area variation between the 4 facelets].
    This function is called on each of the cube sides, therefore the return relates to the face under analysis.""" 
    
    min_area = int(0.08*(w*h)/4)          # min area limit for a single facelet's contour
    max_area = 6*min_area                 # max area limit for a single facelet's contour
    
    # notes:
    # it is like a square when min side/max side < square_ratio (0==perfect square, 1 is rather permissive)
    # considered like a square when diagonal1/diagonal2 > rhombus_ratio (1==perfect, 0.3 is rather permissive)
         
    area = cv2.contourArea(contour)                                       # area of each passed contour is retrieved
    
    if min_area < area < max_area:                                        # filter out too small and too large contours (areas)
        contour_squeeze = np.squeeze(contour)                             # flattens out the list of list used by contours
        edges_delta, axes_ratio = square_check(contour_squeeze)           # sanity check on square and ronbhus shapes
        if edges_delta < square_ratio and axes_ratio > rhombus_ratio:     # check if the contour looks like a square
            cont, in_cont, out_cont = order_4points(contour_squeeze, w, h)  # vertex of each contour are ordered CW from top left
            contour_tmp = [cont]                                          # list is made with the ordered detected contour
            frame = cv2.drawContours(frame, contour_tmp, -1, (255, 255, 255), 1)  # a white polyline is drawn on the contour (1 px thickness)
            if debug:                                                     # case debug variable is set True
                # a white circle is drawn on the 1st vertex (top left), as visual check of proper vertices ordering
                frame = cv2.circle(frame, (contour_tmp[0][0][0],contour_tmp[0][0][1]), 5, (255, 255, 255), -1)
            contour_tmp = [out_cont]                                      # list is made with the ordered outer contour
            frame = cv2.drawContours(frame, contour_tmp, -1, (0, 0, 0), 1)  # a black polyline is drawn on the outer contour (1 px thickness)
            
            M = cv2.moments(contour)                    # the shape moment (center) of the contour is retrieved
            if M['m00']:                                # compute the center of the contour   
                cX = int(M['m10'] / M['m00'])           # X value for the contour center
                cY = int(M['m01'] / M['m00'])           # Y value for the contour center
            
            tmp = {'area': area, 'cx': cX, 'cy': cY, 'contour': contour, 'cont_ordered':in_cont}  # dict with relevant contour info
            facelets.append(tmp)                        # list with the dictionary of the potential facelets contrours
            
            if len(facelets)>=2 and len(facelets)<4:    # case there are 2 or 3 potential contours
                if frameless_cube.lower != 'false':     # case the cube status reading is for frameless cubes or auto (with and without frames)
                    if frameless_cube.lower != 'false' and len(facelets)<4:  # case the cube status reading is for frameless cubes or auto (with and without frames)
                        facelets, frame = estimate_facelets(facelets,frame, w, h)  # calls the function to estimate the remaining facelets  
            
            elif len(facelets)>=4:                      # case there are at least 4 potential contours
                a_to_exclude = area_deviation(facelets, min_area, max_area) # function that analyzes facelets area, and list those with high dev from median
                if len(a_to_exclude)>=1:                # case when there are facelets to be excluded, due to too different area from median one
                    a_to_exclude.sort(reverse=True)     # list order is reversed, making easy easy to remove
                    for i in a_to_exclude:              # contour deviating too much on area are removed from list of potential facelets
                        facelets.pop(i)                 # contour deviating too much on area are removed from list of potential facelets
                left_facelets = len(facelets)-len(a_to_exclude)  # quantity of contours remaining
                if left_facelets >= 2 and left_facelets < 4:   # case there are 2 or 3 potential contours
                    if frameless_cube.lower != 'false':   # case the cube status reading is for frameless cubes or auto (with and without frames)
                        facelets, frame = estimate_facelets(facelets,frame, w, h)  # calls the function to estimate the remaining facelets                                 
    
    return facelets, frame      # list of potential facelet's contour is returned







def facelet_grid_pos(x, y):
    """returns the face facelet number, based on the coordinates of the contour center, and other parameters.
        This is used to map in which facelets a contour has been detected, and which not."""
    
    # Below dict has the face facelets number as value; keys are facelet coordinate expressed as string combination of column and row
    facelet_number = {'11':0, '21':1,
                      '12':2, '22':3}
    
    facelet = str(x) + str(y)                 # facelet string combining column (x) and row (y) of the facelet
    if facelet in facelet_number:             # case the facelecet is in the dict
        return facelet_number[facelet]        # facelet number is returned







def estimate_facelets(facelets, frame, w, h):
    """Estimates the remaing facelets location, when there are at least 2 detected facelets.
        This function is interrupted if one row or one column is fully empty; In this way,
        the cube width and height is known, enabling a good estimation for the missed facelet(s) position(s).
    
    
                x_1     x_2          X
           --|----------------------->
             |       |       |
        y_1  |   1   |   2   |  row 1
             |       |       |
             |----------------
             |       |       |
        y_2  |   3   |   4   |  row 2
             |       |       |
             |----------------
             |
             | clmn1   clmn2
             |  
           Y v
         
    """
    
    
    cont_x = []                                # empty list to fill with contours centers x coordinates
    cont_y = []                                # empty list to fill with contours centers y coordinates
    cont_area = []                             # empty list to fill with contours areas
    facelets_detected = len(facelets)          # number of facelets alerady detected
    
    for i in range(facelets_detected):         # iteration over the quantity of facelets already detected
        cont_x.append(facelets[i]['cx'])       # all the contours centers x coordinates are listed
        cont_y.append(facelets[i]['cy'])       # all the contours centers y coordinates are listed
        cont_area.append(facelets[i]['area'])  # all the contours areas are listed
    
    med_a = int(median(cont_area))             # median area for the facelets in function argument
    
    cx = cont_x.copy()         # list copy of contours centers x coordinates
    cy = cont_y.copy()         # list copy of contours centers y coordinates
    cont_x.sort()              # sorted list with contours centers x coordinates
    cont_y.sort()              # sorted list with contours centers y coordinates
    
    x_1 = []                   # empty list to fill with x coordinates of first column (smaller x)
    x_2 = []                   # empty list to fill with x coordinates of second column (higher x)
    y_1 = []                   # empty list to fill with y coordinates of first row (smaller y)
    y_2 = []                   # empty list to fill with y coordinates of second row (higher y)

    x_low = cont_x[0]          # smaller x coordinate of facelets countours is assigned to the variable x_low
    x_high = cont_x[-1]        # bigger x coordinate of facelets countours is assigned to the variable x_high
    y_low = cont_y[0]          # smaller y coordinate of facelets countours is assigned to the variable y_low
    y_high = cont_y[-1]        # bigger y coordinate of facelets countours is assigned to the variable y_high 
    
    # on the 3x3x3 is divided by 4
    dist = int(max(x_high-x_low, y_high-y_low)/2) # facelets separation distance from min/max detected contours centers
    
    x_1.append(x_low)          # smaller x coordinate of facelets countours is appended to the first column list
    y_1.append(y_low)          # smaller y coordinate of facelets countours is appended to the first row list
    
    for i in range(1, facelets_detected):      # iteration on detected facelets contours
        if x_low <= cont_x[i] and cont_x[i] < x_low + dist:  # case the contour center x coordinate is "small"
            x_1.append(cont_x[i])              # contour x coordinate is appended to the first column list (small x)
        else:                                  # case the contour center x coordinate is "large"
            x_2.append(cont_x[i])              # contour x coordinate is appended to the second column list (large x)
        
        if y_low <= cont_y[i] and cont_y[i] < y_low + dist:  # case the contour center y coordinate is "small"
            y_1.append(cont_y[i])              # contour y coordinate is appended to the first row list (small y)
        else:                                  # case the contour center y coordinate is "large"
            y_2.append(cont_y[i])              # contour y coordinate is appended to the second row list (large y)
    
    if len(x_1)==0 or len(x_2)==0 or len(y_1)==0 or len(y_2)==0 : # case one or more of the four lists are empty
        return facelets, frame                 # function returns the already detected facelets
    
    else:                                      # case no one of the four lists is empty
        x1_avg = int(sum(x_1)/len(x_1))        # average x coordinate for the contours on first column (small x)
        x2_avg = int(sum(x_2)/len(x_2))        # average x coordinate for the contours on second column (large x)
        y1_avg = int(sum(y_1)/len(y_1))        # average y coordinate for the contours on first row (small y)
        y2_avg = int(sum(y_2)/len(y_2))        # average y coordinate for the contours on second row (large y)
    
    dist = int((x_high - x_low + y_high - y_low)/4) # facelets separation distance from min/max detected contours centers
    detected = []                              # list for the column row of the face grid
    for i in range(facelets_detected):         # iteration over the detected facelets
        if cx[i]<x_low+dist:                   # case the facelet contour center x coordinate is on first grid column
            x=1                                # 1 (as column 1) is assigned
        elif cx[i]>x_high-dist:                # case the facelet contour center x coordinate is on second grid column
            x=2                                # 2 (as column 2) is assigned
        else:                                  # case the facelet contour center x coordinate does not fit columns
            x = 0                              # zero is assigned
        if cy[i]<y_low+dist:                   # case the facelet contour center y coordinate is on first grid row                          
            y=1                                # 1 (as row 1) is assigned
        elif cy[i]>y_high-dist:                # case the facelet contour center y coordinate is on second grid row
            y=2                                # 2 (as row 2) is assigned
        else:                                  # case the facelet contour center y coordinate does not fit rows
            y = 0                              # zero is assigned
        detected.append(facelet_grid_pos(x, y))  # list with facelet number is populated
    
    s = set(detected)                          # list with detected facelets numbers is transformed to set
    missed = [x for x in (0,1,2,3) if x not in s]  # list with missed facelets numbers
    
    est = []                                   # list for xy coordinates for the estimated facelet center locations
    for facelet in missed:                     # iteration over the missed facelets numbers
        if facelet == 0:                       # case the missed facelet is 0
            est.append((x1_avg, y1_avg))       # average xy coordinates for column 1 and row 1 are appended
        elif facelet == 1:                     # case the missed facelet is 1
            est.append((x2_avg, y1_avg))       # average xy coordinatees for column 2 and row 1 are appended
        elif facelet == 2:                     # case the missed facelet is 2
            est.append((x1_avg, y2_avg))       # average xy coordinats for column 1 and row 2 are appended
        elif facelet == 3:                     # case the missed facelet is 3
            est.append((x2_avg, y2_avg))       # average xy coordinates for column 2 and row 2 are appended
        else:                                  # case that shouldn't exist
            print("Error on estimating the missed facelets")  # feedback is printed to the terminal

    half = int(0.9*dist/2)                     # half side dimension for the estimated contour square
    for i in range(len(missed)):               # iteration over the missed facelets
        tl = [est[i][0] - half, est[i][1] - half]  # top left contour coordinate, calculated from the estimated contour center point
        tr = [est[i][0] + half, est[i][1] - half]  # top right contour coordinate, calculated from the estimated contour center point
        br = [est[i][0] + half, est[i][1] + half]  # bottom right contour coordinate, calculated from the estimated contour center point
        bl = [est[i][0] - half, est[i][1] + half]  # bottom left contour coordinate, calculated from the estimated contour center point
        pts=np.array([tl, tr, br, bl], dtype="int32")  # estimated contour coordinates      
        
        gap=5                                  # pixels gap
        tl[0]=max(tl[0]-gap,0)                 # top left x coordinate, shifted toward the contour outer side
        tl[1]=max(tl[1]-gap,0)                 # top left y coordinate, shifted toward the contour outer side
        tr[0]=min(tr[0]+gap,w)                 # top right x coordinate, shifted toward the contour outer side
        tr[1]=max(tr[1]-gap,0)                 # top right y coordinate, shifted toward the contour outer side
        br[0]=min(br[0]+gap,w)                 # bottom right x coordinate, shifted toward the contour outer side
        br[1]=min(br[1]+gap,h)                 # bottom right y coordinate, shifted toward the contour outer side
        bl[0]=max(bl[0]-gap,0)                 # bottom left x coordinate, shifted toward the contour outer side
        bl[1]=min(bl[1]+gap,h)                 # bottom left y coordinate, shifted toward the contour outer side
        outer_pts=np.array([tl, tr, br, bl], dtype="int32")    # estimated contour coordinates, sligtly shifted toward the contour outer side
        
        contour_tmp = [pts]                    # list is made with the ordered outer contour
        frame = cv2.drawContours(frame, contour_tmp, -1, (0, 0, 0), 1)        # a black polyline is drawn on the contour (1 px thickness)
        contour_tmp = [outer_pts]              # list is made with the ordered outer contour
        frame = cv2.drawContours(frame, contour_tmp, -1, (255, 255, 255), 1)  # a white polyline is drawn on the outer contour (1 px thickness)

        tmp = {'area': med_a, 'cx': est[i][0], 'cy': est[i][1], 'contour': pts, 'cont_ordered':pts} # dict with relevant contour info
        facelets.append(tmp)                   # estimated facelets relevant info are appended to the detected facelets list
    
    if screen and debug and frameless_cube!=False:  # case there is a connected screen, debug and Frameless_cube not False
        x_avg = int((x1_avg + x2_avg)/2)       # average x coordinate
        y_avg = int((y1_avg + y2_avg)/2)       # average y coordinate
        cv2.line(frame, (x_avg, 0), (x_avg, h), (255, 255, 255), 2)  # vertical line is drawn between first and second row of facelets
        cv2.line(frame, (0, y_avg), (w, y_avg), (255, 255, 255), 2)  # horizontal line is drawn between first and second column of facelets
        
    return facelets, frame                     # detected facelets combined with estimated facelets







def get_facelets_fcs(facelets, frame):
    """This function points to fix coordinates at the cube face image, to retrieve the color.
        Dummy contours are made, to visualize them on screen, or saved picture_collage, when debug is true."""
    
    if debug:
        print("Called the fix_coordinate_approach")
        
    c = f_coordinates                          # f_coordinates assigned to a local very short variable name
    
    # x and y distance between the facelets coordinates
    x_dist = (c[2]-c[0] + c[6]-c[4])/2
    y_dist = (c[5]-c[1] + c[7]-c[3])/2
    
    s_side_x = int(round(0.6*x_dist/2,0))      # half side dimension, along x, for the estimated contour square
    s_side_y = int(round(0.6*y_dist/2,0))      # half side dimension, along y, for the estimated contour square                    
    
    area = s_side_x*s_side_y*4                 # estimated area
    for i in range(0,8,2):                     # iteration over the 4 facelets
        tl = [c[i] - s_side_x, c[i+1] - s_side_y]  # top left contour coordinate, calculated from the fix coordinate center point
        tr = [c[i] + s_side_x, c[i+1] - s_side_y]  # top right contour coordinate, calculated from the fix coordinate center point
        br = [c[i] + s_side_x, c[i+1] + s_side_y]  # bottom right contour coordinate, calculated from the fix coordinate center point
        bl = [c[i] - s_side_x, c[i+1] + s_side_y]  # bottom left contour coordinate, calculated from the fix coordinate center point
        pts=np.array([tl, tr, br, bl], dtype="int32")  # estimated contour coordinates      
        
        gap=3                                  # pixels gap
        tl[0]=max(tl[0]-gap,0)                 # top left x coordinate, shifted toward the contour outer side
        tl[1]=max(tl[1]-gap,0)                 # top left y coordinate, shifted toward the contour outer side
        tr[0]=min(tr[0]+gap,w)                 # top right x coordinate, shifted toward the contour outer side
        tr[1]=max(tr[1]-gap,0)                 # top right y coordinate, shifted toward the contour outer side
        br[0]=min(br[0]+gap,w)                 # bottom right x coordinate, shifted toward the contour outer side
        br[1]=min(br[1]+gap,h)                 # bottom right y coordinate, shifted toward the contour outer side
        bl[0]=max(bl[0]-gap,0)                 # bottom left x coordinate, shifted toward the contour outer side
        bl[1]=min(bl[1]+gap,h)                 # bottom left y coordinate, shifted toward the contour outer side
        outer_pts=np.array([tl, tr, br, bl], dtype="int32")     # estimated contour coordinates, sligtly shifted toward the contour outer side
        
        contour_tmp = [pts]                    # list is made with the ordered outer contour
        frame = cv2.drawContours(frame, contour_tmp, -1, (0, 0, 0), 1)        # a black polyline is drawn on the contour (1 px thickness)
        contour_tmp = [outer_pts]              # list is made with the ordered outer contour
        frame = cv2.drawContours(frame, contour_tmp, -1, (255, 255, 255), 1)  # a white polyline is drawn on the outer contour (1 px thickness)

        tmp = {'area': area, 'cx': c[i], 'cy': c[i+1], 'contour':pts, 'cont_ordered':pts} # dict with relevant contour info
        facelets.append(tmp)                   # estimated facelets relevant info are appended to the detected facelets list
    
    return facelets, frame     # facelets info, based on fix coordinates, are returned






def area_deviation(data, min_area, max_area):
    """ Checks whether the areas of 4 facelets are within a pre-defined deviation from the median one
    This function is called when there are a pre-defined amount of potential facelet contours
    Argument is a list of dictionary, wherein the area is one of the dict values
    Returns a list of facelets (index) to be removed from the potential facelets, having area deviating
    too much from the median one."""

    
    to_exclude = []                  # list of the contours index to be removed, due to excess of their area deviation
    # delta_area_limit = 0.7         # 70% of area deviation from the median is set as threshold (quite permissive)
    area_list = []                   # list to store the contour areas
    
    for i in range(len(data)):
        area_list.append(data[i]['area'])                       # all the contour areas are listed
        if debug:                                               # case debug variable is set True
            print("Contours areas detected:",area_list)         # feedback is printed to the terminal

    area_median = median(area_list)                             # median area values
    for i in range(len(area_list)):                             # iteration over the facelets areas received
        delta_area=abs((area_list[i]-area_median)/area_median)  # area deviation from the median
        if delta_area > delta_area_limit:                       # filter on area deviating more than threshold
            to_exclude.append(i)                                # list of the contours to exclude is populated
            if debug:                                           # case debug variable is set True
                print('Removed contour with area: ',area_list[i], " having delta_area of:",delta_area) # feedback is printed to the terminal

    if debug:                                                   # case debug variable is set True
        if len(to_exclude)==0 and len(area_list)>=4:            # case all the face facelets have been detected
            if side == 1:                                       # case the face is the first one (U)
                print("Acceptable facelets area from min:",min_area, ",  to max:", max_area, ", with max area_delta <=", delta_area_limit)
            print("Median facelets area:", area_median, "\tareas min:", min(area_list), "\tareas_max:", max(area_list))  # feedback is printed to the terminal
            print("Minimum facelet area delta vs median:", round(abs((min(area_list)-area_median)/area_median),2))       # feedback is printed to the terminal
            print("Maximum facelet area delta vs median:", round(abs((max(area_list)-area_median)/area_median),2))       # feedback is printed to the terminal
            print()
                      
    return to_exclude                # returns list of contours to be removed







def order_4points(pts, w, h):
    """ Based on: https://www.pyimagesearch.com/2016/03/21/ordering-coordinates-clockwise-with-python-and-opencv/
    Modified to only use Numby instead of Scipy library.
    This function orders the 4 vertex of (simplified) contours, so that the first one is top left (CW order).
    Argument is a contour.
    Function returns a contour with coordinates ordered as per below sketch.
    
    0 ______ 1
     |      |
     |      |
     |______|
    3        2
    
    """
    
    xSorted = pts[np.argsort(pts[:, 0]), :]        # sort the points based on their x-coordinates
    leftMost = xSorted[:2, :]                      # grab the left-most point from the sorted x-coodinate points
    rightMost = xSorted[2:, :]                     # grab the right-most point from the sorted x-coodinate points
    
    # sort the left-most according to their y-coordinates, to grab the top-left and bottom-left points, respectively
    (tl, bl) = leftMost[np.argsort(leftMost[:, 1]), :]
    
    # Euclidean distance from top-left and right-most points: the point with largest distance will be bottom-right
    D = tl.reshape(1, 2)[:, np.newaxis, :] - rightMost[np.newaxis, :, :]   # matrix difference, by broadcasting tl and rightMost
    D = np.linalg.norm(D, axis=-1)[0]                                      # matrix distance of all rightMost vertices from tl
    
    (br, tr) = rightMost[np.argsort(D)[::-1], :]
    pts=np.array([tl, tr, br, bl])         # CW ordered coordinates, from top left, of the detected contour
    
    gap=3                                  # pixels for contour shifting toward inside and outside
    tl[0]=min(tl[0]+gap,w)                 # top left x coordinate, shifted toward the contour inner side
    tl[1]=min(tl[1]+gap,h)                 # top left y coordinate, shifted toward the contour inner side
    tr[0]=max(tr[0]-gap,0)                 # top right x coordinate, shifted toward the contour inner side
    tr[1]=min(tr[1]+gap,h)                 # top right y coordinate, shifted toward the contour inner side
    br[0]=max(br[0]-gap,0)                 # bottom right x coordinate, shifted toward the contour inner side
    br[1]=max(br[1]-gap,0)                 # bottom right y coordinate, shifted toward the contour inner side
    bl[0]=min(bl[0]+gap,w)                 # bottom left x coordinate, shifted toward the contour inner side
    bl[1]=max(bl[1]-gap,0)                 # bottom left y coordinate, shifted toward the contour inner side
    inner_pts=np.array([tl, tr, br, bl], dtype="int32")   # ordered coordinates, sligtly shifted toward the contour inner side
    
    gap=2*gap                              # pixels gap is doubled as it now refers to coordinates already shifted toward the inside
    tl[0]=max(tl[0]-gap,0)                 # top left x coordinate, shifted toward the contour outer side
    tl[1]=max(tl[1]-gap,0)                 # top left y coordinate, shifted toward the contour outer side
    tr[0]=min(tr[0]+gap,w)                 # top right x coordinate, shifted toward the contour outer side
    tr[1]=max(tr[1]-gap,0)                 # top right y coordinate, shifted toward the contour outer side
    br[0]=min(br[0]+gap,w)                 # bottom right x coordinate, shifted toward the contour outer side
    br[1]=min(br[1]+gap,h)                 # bottom right y coordinate, shifted toward the contour outer side
    bl[0]=max(bl[0]-gap,0)                 # bottom left x coordinate, shifted toward the contour outer side
    bl[1]=min(bl[1]+gap,h)                 # bottom left y coordinate, shifted toward the contour outer side
    outer_pts=np.array([tl, tr, br, bl], dtype="int32")   # ordered coordinates, sligtly shifted toward the contour outer side

    return pts, inner_pts, outer_pts







def order_4contours(data, new_center):
    """ Based on: https://www.pyimagesearch.com/2016/03/21/ordering-coordinates-clockwise-with-python-and-opencv/
    Modified to only use Numby instead also Scipy library.
    This function orders the 4 countorus centers, with first one on top left, and order as per below sketch:
    -----------------
    |       |       |
    |   0   |   1   | 
    |       |       |
    |----------------
    |       |       |
    |   2   |   3   | 
    |       |       |
    |----------------
 
     """
    
    pts=np.zeros([4,2], dtype=int)                 # numpy array of zeros, having 4 items of two entries
    for i in range(len(data)):                     # iteration over the (4) facelets coordinates
        pts[i]=[data[i]['cx'], data[i]['cy']]      # numpy array is filled with the facelets centers coordinates
        
    xSorted = pts[np.argsort(pts[:, 0]), :]        # sort all the points based on their x-coordinates
    leftMost = xSorted[:2, :]                      # grab the left-most 2 points from the sorted x-coodinate points
    rightMost = xSorted[2:, :]                     # grab the right-most 2 points from the sorted x-coodinate points
    
    # sort the 2 left-most points according to their y-coordinates, to grab the top/bottom one respectively
    leftMost = leftMost[np.argsort(leftMost[:, 1]), :]
    (tl, bl) = leftMost
    
    # Euclidean distance from top-left and right-most points: the point with largest distance will be bottom-right
    D = tl.reshape(1, 2)[:, np.newaxis, :] - rightMost[np.newaxis, :, :]   # matrix difference, by broadcasting tl and rightMost
    D = np.linalg.norm(D, axis=-1)[0]                                      # matrix distance of all rightMost vertices from tl
    
    # sort the right-most according to their distance from top-left coordinate
    (br, tr) = rightMost[np.argsort(D)[::-1], :]
    
    ordered_points = np.array([tl, tr, bl, br], dtype="int32")   # ordered coordinates (centers of 4 facelets)   
    
    for coordinates in ordered_points:
        for i in range(len(data)):
            if data[i]['cx'] == coordinates[0] and data[i]['cy'] == coordinates[1]:        
                new_center.append(data[i])        # new_center is a new list with data ordered by xy coordinates
                data.pop(i)                       # used data-element is removed to speed up next iterations
                break                             # inner for loop can be break once the if found and data appended

    return new_center







def save_coordinates(coordinates):
    """Saves the coordinates of the 4 facelets to a text file.
        This action is done when a cubes_status is correctly determined.
        The 4 coordinates are averaged from the 6 faces."""
    
    coordinates = np.array(coordinates)                     # the coordinates list is converted to numpy array 
    avg = coordinates.mean(axis=0)                          # coordinates are averaged by 'columns'
    avg = np.round(avg, decimals=0).astype(int)             # coordinates are first rounded to 0 decimal then converted to integers
    avg = str(list(avg))                                    # coordinates are converted from array to list to string
    avg = avg.replace('[','').replace(']','').replace(' ','')+'\n'  # coordinates string without parentheses and empty spaces
    fname = 'Cubotino_P_coordinates.txt'                    # fname for the text file to retrieve the coordinates
    folder = pathlib.Path().resolve()                       # active folder (should be home/pi/cubotino_pocket/src)
    fname = os.path.join(folder, fname)                     # folder and file name for the coordinates, to be saved
    with open (fname, 'a') as f:                            # text file is opened to write on it in 'appending' mode
        f.write(avg)                                        # coordinates are saved to text file







def load_coordinates():
    """Loads the coordinates of the 4 facelets from a text file.
        Checks if all the characters in file are valid, else remove lines with non valid characters."""
    
    lines = []                                              # empty list to store the data from the file, or to return is empty
    historical_data = False                                 # flag to track presence of historical data is set False
    fname = 'Cubotino_P_coordinates.txt'                    # fname for the text file to retrieve the coordinates
    folder = pathlib.Path().resolve()                       # active folder (should be home/pi/cubotino_pocket/src) 
    fname = os.path.join(folder, fname)                     # folder and file name for the coordinates, to be loaded
    
    if os.path.exists(fname):                               # case the coordinates file exists
        with open(fname, "r") as f:                         # settings file is opened in reading mode
            lines = f.read().splitlines()                   # all lines (without LF) are assigned as list to lines variable
        if len(lines)>=1:                                   # case the file has at least one row of data
            historical_data = True                          # flag to track presence or assence of historical data is set True
    else:                                                   # case the coordinates file does not exist
        print(f"Not found file {fname}")                    # print feedback to the terminal
        print("This files is generated by the robot at the first successfull cycle") # print feedback to the terminal

    corrupted_data = False                                  # corrupted_data is initially set False
    if len(lines)>=1:                                       # case the file has at least one row of data
        lines = [line.replace(' ', '') for line in lines]   # all spaces are removed
        valid_chars = set('0123456789,')                    # set of valid charcters (includes comma)
        for line in lines:                                  # iteration through the lines
            for c in line:                                  # iteration through the characters in line
                if c not in valid_chars:                    # case the character is not valid
                    corrupted_data = True                   # corrupted_data is set True
                    break                                   # inner for_loop s interrupted
            if corrupted_data:                              # case corrupted_data is True
                break                                       # outer loop_is interrupted
       
    if corrupted_data:                                      # case corrupted_data is True
        if debug:                                           # case debug is set true
            print(f"\nNot valid characters in {fname}")     # feedback is printed to the terminal
        new_lines=[]                                        # empty list to store the cleaned lines
        with open(fname, "w") as f:                         # settings file is opened in writing mode
            for line in lines:                              # iteration through the lines
                if not line.isspace():                      # case the line is not empty
                    keep_line=True                          # keep_line variable is initially set True
                    for c in line.strip().strip('\n'):      # iteration through the characters in line
                        if c not in valid_chars:            # case the character is not valid
                            keep_line=False                 # keep_line variable is set False
                            break                           # inner for_loop is interrupted
                    if keep_line:                           # case keep_line variable is (still) True
                        f.write(line)                       # that line is written to text file
                        new_lines.append(line)              # line is appended to lines
        
        if len(new_lines)>=1:                               # case the file has at least one row of data
            lines = new_lines                               # new_lines is assigned to lines
            if debug:                                       # case debug is set true
                print(f"The file got repaired")             # feedback is printed to the terminal
        else:                                               # case the remaining file does not have any row of data
            lines=[]                                        # lines variable is set as an empty list
            historical_data = False                         # historical data variable is set False
        
    if historical_data:                                     # case there is historical data
        # convert from string to integers and feed a list with coordinates values as tuple
        all_coordinates = []                                # empty list to store all the coordinates (prevoius solves cubes)
        for line in lines:                                  # iterating on each set of coordinates (each cube)
            coordinates=[]                                  # empty list to store the coordinated parsed from text to integers
            for i in range(7):                              # iterating over the 4 facelets of each cube set of coordinates
                val = int(line[: line.find(',')])           # coordinate is retrieved and converted to integer
                line = line[line.find(',')+1:]              # line is sliced for the remaining coordinates
                coordinates.append(val)                     # facelet coordinate is appended to the coordinates list
            coordinates.append(int(line))                   # the last facelet is appended to the coordinates list
            all_coordinates.append(coordinates)             # all the facelet coordinates are appended to all_coordinates list variable
        
        # limits the dataset to latest 5 cube readings saved (latest scans are more relevant, in case of settings changed at robot)
        n = len(all_coordinates)                            # quantity of coordinates sets (cubes) stored
        if n > 5:                                           # case there are more than 5 sets of coordinates (more than 5 cubes' history)
            all_coordinates = all_coordinates[-5:]          # only the last 5 are considered
        if n > 10:                                          # case there are more than 30 sets of coordinates (more than 5 cubes' history)
            remove_old_data(fname)                          # call a function that removes old data from the text file
        
        # average the coordinates from the dataset
        all_coordinates = np.array(all_coordinates)         # the list of lists all_coordinates is changed to a 2d numpy array
        avg = all_coordinates.mean(axis=0)                  # coordinates are averaged by 'columns'
        avg = np.round(avg, decimals=0).astype(int)         # coordinates are first rounded to 0 decimal then converted to integers
        avg = avg.tolist()                                  # coordinates are assigned to a list
        if debug:                                           # case debug is set true
            print("Loaded facelets coordinates:", avg)      # feedback is printed to the terminal
        return avg                                          # the average coordinates are returned
    
    else:                                                   # case there isn't historical data
        if debug:                                           # case debug is set true
            print("Not loaded facelets coordinates")        # feedback is printed to the terminal
        return []                                           # an empty list is returned 








def remove_old_data(fname):
    """"Removes excess data from the coordinates file (it keeps the last 10 rows)."""
    
    with open(fname, "r") as f:                             # settings file is opened in reading mode
        lines = f.readlines()                               # all lines are assigned as list to lines variable
        lines = lines[-5:]                                  # the last 5 lines are assigned to a local variable
    
    with open (fname, 'w') as f:                            # text file is opened to write on it (to empty it)
        f.write('')                                         # an empty character is saved
    
    with open (fname, 'a') as f:                            # text file is opened to write on it, in appending mode
        for line in lines:                                  # iteration over the lines variable
            f.write(line)                                   # line is written to file
    
    if debug:                                               # case debug is set true
        print(f"\nRemoved excessive data from {fname}")     # feedback is printed to the terminal







def cube_colors_clusters(color, vectors, clusters):
    """ This function is used to divide the facelets' colors in 6 clusters.
        The argumnent is the mean color values (BR or HSV) for the 24 facelets detected on the cube.
        The funtion returns a numpy array with the 6 dominant colors. """
    
    facelets_color = np.array(color)                          # facelets BGR_mean colors changed to array
    reshaped_facelets = facelets_color.reshape((-1,vectors))  # facelets BGR_mean colors array to single vector
    reshaped_facelets = np.float32(reshaped_facelets)         # facelets BGR_mean colors array to float 32 bit
    criteria = (cv2.TERM_CRITERIA_EPS + cv2.TERM_CRITERIA_MAX_ITER, 10, 1.0)  # escape criteria for clustering (epsilon and max iterations)
    clusters = clusters                                       # number of clusters (obviously the 6 colors of the cube)
    ret, label, ref_colors = cv2.kmeans(reshaped_facelets, clusters, None, criteria, 5, cv2.KMEANS_RANDOM_CENTERS)  # colors clustering
    return label, ref_colors







def cube_colors_interpr_BGR(BGR_detected, ref_colors_BGR):
    """ This function is used to define the cube status.
    The basic principle is to associate facelets to the reference color having the minimum color distance.
    From the mean BGR color, detected per each facelet, the euclidean distance is calculated toward the 6 reference colors.
    The 6 reference colors are the 6 dominant colors, out of the 24 facelets.
    After completing this process, for all the facelets, the interpreted colors have to be ordered back to URFDLB order.
    
    Note: On a 3x3x3 cube, the cube status is defined by letters indicating tha face (i.e. U, R, F); In this case the letters
    refer to the the face having the center of that specific color.
    On a 2x2x2 cube, the cube status is also defined by letters: In this case the letters do not have a cube face meaning."""
    
    
    cube_status_error = False
    
    # Step1: dict with BGR_detected and facelet's position as key
    BGR_detected_dict={}                                    # empty dict to store the average BGR values detected per each facelet
    for i in range(len(BGR_detected)):                      # iteration over the (expected 54) elemnt is list with avg BGR detected 
        BGR_detected_dict[i]=BGR_detected[i]                # BGR detected on facelet i is assigned to the dict, having the facelet i as key
    
    if debug:                                               # case debug variable is set True
        print(f'\nBGR_detected: {BGR_detected}')            # feedback is printed to the terminal

    # Step2: BGR of the 6 dominat colors, out of the detected 24 facelets, are used as reference
    cube_ref_colors = {'c0':ref_colors_BGR[0], 'c1':ref_colors_BGR[1], 'c2':ref_colors_BGR[2],
                       'c3':ref_colors_BGR[3], 'c4':ref_colors_BGR[4], 'c5':ref_colors_BGR[5]}
    
    # Step3: dictionary with the color distances from the references
    color_distance={}                                             # empty dict to store all the color distances for all the facelets
    cube_ref_colors_lab={}                                        # empty dictionary to store color refences in Lab color space
    for color, BGR in cube_ref_colors.items():                    # iteration over the 6 centers
        B,G,R = BGR                                               # BGR values are unpact from the dict
        cube_ref_colors_lab[color]=tuple(rgb2lab([R,G,B]))        # BGR conversion to lab color space and dict feeding
            
    for facelet, color_measured in BGR_detected_dict.items():     # iteration over the 54 facelets
        B,G,R = color_measured                                    # individual BGR components
        lab_meas = rgb2lab([R,G,B])                               # conversion to lab color space (due CIEDE2000 function)
        distance=[]                                               # list with the distance from the 6 references, for each facelet
        for color, lab_ref in cube_ref_colors_lab.items():        # iteration over the 6 reference colors
            distance.append(CIEDE2000(tuple(lab_meas), lab_ref))  # Euclidean distance toward the 6 reference colors
        color_distance[facelet]=distance   # dict (facelet num as key) is populated with the measured distance from the 6 centes
    
    
    # Step4: Ordering the color distance (the min value per each facelet) by increasing values
    color_distance_copy=color_distance.copy()                     # a dict copy is made, to drop items while the analysis progresses
    color_distance_ordered={}                                     # empty dictiony to store the (min) color distance by increasing values
    for i in range(len(color_distance_copy)):                     # iteration over the dict copy
        key_min_dist = min(color_distance_copy,key=lambda key:min(color_distance_copy[key])) # dict key for the facelet with smaller color dist
        color_distance_ordered[key_min_dist] = color_distance_copy[key_min_dist]  # dict with facelets ordered by smaller distance, is populated
        color_distance_copy.pop(key_min_dist)   # removed the facelet from the dic copy, to search the next facelect with smaler color distance
    
    
    # Step5: List with facelets position ordered according to the color distance increasing order
    # this is needed to come back later to original URFDLB facelets order
    key_ordered_by_color_distance = [x for x in color_distance_ordered.keys()]


    # Step6: Ordering the facelets BGR color values according to color distance from the reference colors
    BGR_ordered={}
    for key in color_distance_ordered.keys():
        BGR_ordered[key]=BGR_detected[key]    # key is always the facelet number, yet the ordered dict is by increasing color distance


    # Step7: Color interpretation
    cube_status_by_color_distance={}          # dict to store the cube status reppresentation wih the interpreted colors
    distance={}                               # dict to store the color distance during each facelet check
    full_cube=['c0','c1','c2','c3','c4','c5']*4
    for i, value in enumerate(BGR_ordered.values()):        # iteration on the facelet's BGR values ordered by increasing color distance from ref
        B,G,R = value
        lab_meas = rgb2lab([R,G,B])                         # conversion to lab color space (due CIEDE2000 function)
        for color, lab_ref in cube_ref_colors_lab.items():  # iteration over the 6 reference colors
            distance[color]=CIEDE2000(tuple(lab_meas), lab_ref)  # Euclidean distance toward the 6 reference colors
        color = min(distance, key=distance.get)             # chosen color is the one with min distance from reference
        cube_status_by_color_distance[i] = color            # chosen color is assigned to the facelet 'i'
        distance.clear()                                    # distance dict is cleared for the next facelet
        
        # Cube detection status is validated by expecting 4 facelets per each of the 6 colors
        if color in full_cube:                              # case the chosen color is listed on those left at full_cube
            full_cube.remove(color)                         # the assigned color is removed from the full_cube list
            if i == 22:                                     # case all but one facelets have ben assigned
                cube_status_by_color_distance[23] = full_cube[0]  # the last color left is assigned to the last facelet
                break                                       # for loop is interrupted
        else:                                               # case the chosen color is not anymore available
            cube_status_error = True                        # cube_status_error is set True to enable a different analysis
    
    
    # Step8: Cube detection status is generated (a dict having the facelet number as key and the color as value)
    cube_status={}                                          # dict to store the facelet number as key and the color as value 
    if not cube_status_error:                               # case there are 4 facelets per each of the 6 colors
        for i in range(24):                                 # iteration over the 24 facelets
            cube_status[i]=cube_status_by_color_distance[key_ordered_by_color_distance.index(i)] # dict with facelet as key and color as value
    else:
        if debug:                                           # case debug is set True
            print()                                         # print an empty line
            print('#'*55)                                   # print a separation line
            print("Error in the cube status detection, via BGR color space")  # feedback is printed to the terminal
            print('#'*55)                                   # print a separation line
            print()                                         # print an empty line
        else:                                               # case debug is set False
            print("\nError in the cube status detection, via BGR color space")  # feedback is printed to the terminal
        
    return cube_status







def cube_colors_interpr_HSV(HSV_detected):
    """This function uses on the HSV color space, converted from the avg BGR read on facelets.
    It determines the colors assigned to all facelets, based on HSV value measured.
    The argument is a list with 24 entries of the [H,S,V] for the average color detected at the facelets centers.
    Baseline:  All facelets are evaluated only by their H (Hue) value.
               Dominant Hue values are used as reference.
    There is no interpretation of the colors from the Hue values, just clustering.
    This function returns the interpreted facelet colors, on the URFDLB order.""" 
    
    print()                                                 # print an empty line
    print('#'*65)                                           # print a separation line
    print('Called the function to get the cube status vis HSV color analysis') # feedback is printed to the terminal
    print('#'*65)                                           # print a separation line
    print()                                                 # print an empty line

    if debug:                                               # case debug variable is set True
        print("\nHSV_detected:", HSV_detected)              # feedbacl is printed to the terminal

    clusters = 6                                            # number of clusters in this analysis type
    
    # Step1, generate sone dictionaries
    Hue = {}                                                # dict to store the Hue value of all facelets
    S = {}                                                  # dict to store the S (Saturation) value of all facelets
    V = {}                                                  # dict to store the V (Value)  of all facelets
    VSdelta={}                                              # dict to store the V-S (value-Saturation) value of all facelets
    for facelet, hsv in enumerate(HSV_detected):            # Hue, Saturation and Value are retrieved from the HSV dict
        Hue[facelet] = hsv[0]                               # Hue is assigned to the Hue dict
        S[facelet] = hsv[1]                                 # Satuartion is assigned to the S dict
        V[facelet] = hsv[2]                                 # Value is assigned to the V dict



    # Step2: get the Hue of the 6 dominant colors, out of the detected 24 facelets
    Hue_detected = list(Hue.values())                       # list the Hue of the detected 24 facelets
    label, Hue_ref = cube_colors_clusters(Hue_detected, vectors=1, clusters=clusters)  # 6 reference Hue colors, out of the 24 colored facelets
    Hue_reference = [x[0] for x in np.uint8(Hue_ref).tolist()]  # Hue_ref is converted to int to list and assigned to Hue_reference 
    if debug:                                               # case debug variable is set True
        print("\nHue colors:", Hue)                         # feedback is printed to the terminal
    
    
    
    # Step3: check if clusters have 4 values each
    label_list = [x[0] for x in label.tolist()]             # list with the clustered labels for the 20 colored facelets
    if debug:                                               # case debug variable is set True
        print("\nClusters labels:", label_list)             # feedback is printed to the terminal
        
    clustering_ok = True                                    # boolean clustering_ok to track the clustering result
    max_k = 0                                               # zero is assigned to max_k (largest cluster)
    for i in range(clusters):                               # iteration over the clusters quantity
        n = label_list.count(i)                             # occurrences of label(i) is assigned to variable n
        max_k = max(max_k, n)                               # max_k is updated if a large n is found
        if n != 4:                                          # case a cluster is not equal to 4 (as it should be when correct)
            clustering_ok = False                           # clustering_ok is set False
    
    hue_range = max(Hue.values()) - min(Hue.values())       # Hue range is calculated
    if max_k >= 8 or hue_range < 50:                        # case the largest cluster has at least 8 entries or small Hue_range
        clustering_ok = True  # clustering_ok is set True to enable the alternative analysis while not worth reorganizing the clustering
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
