AndreaFavero71/cubotino_pocket/src/Cubotino_P_moves.py

#!/usr/bin/python
# coding: utf-8

"""
#############################################################################################################
# Andrea Favero 11 February 2024
# 
# From Kociemba solver to robot moves
# This applies to CUBOTino Pocket, a simple Rubik's cube solver robot
# This version is specific for the 2x2x2 Rubik's cube version (Pocket)
#
# The Kociemba cube solver returns a solution that has to be translated into robot movements
# Notations for faces are as per URF notations: U=Up, R=Right, F=Front, D=Down, L=Left, B=Back
# Tipically the solver considers the cube orientation to don't change while solving it....
# On this simpler robot, the mechanical constraints (servo rotation limited to 180deg), suggests a different approach:
#  - The face to be turned, according to the solver, will be adapted to reflect the side such face is located
#  - This means a supposed R1 might change L1 if the left cube side is located on the right side at that moment in time
# Amount of robot movements increases by about 85% because of these mechanical contraints
#
#
# Possible moves with this robot
# 1) Spins the complete cube ("S") laying on the bottom face: 1 means CW 90deg turns, while 3 means 90CCW turn
# 2) Flips the complete cube ("F") by "moving" the Front face to Bottom face: Only positive values are possible
# 3) Rotates the bottom layer ("R") while costraining the 2nd and 3rd layer.
# 4) The order of S, F has to be strictly followed
# 5) Example 'F1R1S3' means: 1x cube Flip, 1x (90deg) CW rotation of the 1st (Down) layer, 1x (90deg) CCW cube Spin 
#
#############################################################################################################
"""


# Global variable
# Below dict has all the possible robot movements, related to the cube solver string
moves_dict = {'U1':'F2R1S3', 'U2':'F2R1S3R1S3', 'U3':'F2S1R3',
              'D1':'R1S3',   'D2':'R1S3R1S3',   'D3':'S1R3',
              'F1':'F1R1S3', 'F2':'F1R1S3R1S3', 'F3':'F1S1R3',
              'B1':'F3R1S3', 'B2':'F3R1S3R1S3', 'B3':'F3S1R3',
              'L1':'S3F3R1', 'L2':'S3F3R1S3R1', 'L3':'S1F1R3',
              'R1':'S3F1R1', 'R2':'S3F1R1S3R1', 'R3':'S1F3R3'}







def starting_cube_orientation(simulation=False):
    """ Cube orientation at the start, later updated after every cube movement on the robot
        Dict key is the the "stationary" side, while the dict value is the cube side
        
        After scanning the cube is not URF oriented.
        When simulating, the cube is considered as URF facing Up Right Front.
        By knowing 5 faces, the 6th face is also known ;-)
        
        
        Case of simulation:
        v_faces{}   _______       
                   |       |
                   | ['U'] |
                   |_______|     h_faces{}  _______ _______ _______ 
                   |       |               |       |       |       |
                   | ['F'] |               | ['L'] | ['F'] | ['R'] |
                   |_______|               |_______|_______|_______|
                   |       |
                   | ['D'] |
                   |_______|    

        
        
        Cube orientation after scanning (no simulation):
        v_faces{}   _______       
                   |       |
                   | ['L'] |
                   |_______|     h_faces{}  _______ _______ _______ 
                   |       |               |       |       |       |
                   | ['U'] |               | ['F'] | ['U'] | ['B'] |
                   |_______|               |_______|_______|_______|
                   |       |
                   | ['R'] |
                   |_______|
        
        
        
        Cubie numbering, to track the DBL corner
        dbl cubie is at 6 (not visible on below sketch) when the cube is URF oriented
        dbl cubie is at 2 when the cube after scanning
             ______________ 
            /1     /     2/|
           /______/______/ |
          /      /      /| |
         /3_____/_____4/ | |
         |      |      | |/|
         |      |      | | | 
         |______|______|/| 6
         |      |      | |/
         |      |      | /
         |7_____|_____8|/
        
        
        """
    
    
    global h_faces,v_faces, dbl             # global variables used
    
    if simulation:                          # case simultion is set True
        # Cube orientation at the start (UFR), later updated after every cube movement on the robot
        h_faces={'L':'L','F':'F','R':'R'}   # dict with faces around the bottom/upper positioned faces
        v_faces={'U':'U','F':'F','D':'D'}   # dict with faces around the left/right positioned faces
        dbl = 5                             # dbl cubie at start (cube as URF)
    
    elif not simulation:                    # case this function is called after scanning the cube
        # Cube orientation after scanning, later updated after every cube movement on the robot
        h_faces={'L':'F','F':'U','R':'B'}   # dict with faces around the bottom/upper positioned faces
        v_faces={'U':'L','F':'U','D':'R'}   # dict with faces around the left/right positioned faces
        dbl = 2                             # dbl cubie at start (cube after the scanning)
    

    
    


def opp_face(face):
    """ This function returns the opposite face of the one in argument."""
    
    if face == 'F': return 'B'              # case face is F its returned opposite is B
    elif face == 'B': return 'F'            # case face is B its returned opposite is F
    elif face == 'U': return 'D'            # case face is U its returned opposite is D
    elif face == 'D': return 'U'            # case face is D its returned opposite is U
    elif face == 'R': return 'L'            # case face is R its returned opposite is L
    elif face == 'L': return 'R'            # case face is L its returned opposite is R
    else:                                   # case face is not captured on above cases
        return 'Error'                      # error string is returned






def flip_effect(h_faces,v_faces):
    """ Returns the cube faces orientation after a single Flip action; Only v_faces are affected
        It applies a face shift of these faces, and updates the F face on the h_faces dict."""
    
    global dbl                              # global dbl is used
    v_faces['D']=v_faces['F']               # vertical face shift
    v_faces['F']=v_faces['U']               # vertical face shift
    v_faces['U']=opp_face(v_faces['D'])     # vertical face shift, via opposite face
    h_faces['F']=v_faces['F']               # vertical face shift
    dbl=flip_dbl(dbl)                       # dbl cubie location is updated






def flip_dbl(dbl):
    """ Returns the dbl cubie position after a Flip."""
    
    if dbl==1 or dbl==2:                    # case dbl cubie is at 1 or 2
        dbl += 2                            # cubie is shifted by +2
    elif dbl==3 or dbl==4:                  # case dbl cubie is at 3 or 4
        dbl += 4                            # cubie is shifted by +4
    elif dbl==5 or dbl==6:                  # case dbl cubie is at 5 or 6
        dbl -= 4                            # cubie is shifted by -4
    elif dbl==7 or dbl==8:                  # case dbl cubie is at 7 or 8
        dbl -= 2                            # cubie is shifted by -2
    return dbl                              # shifted dbl cubie is returned







def spinCCW_effect(h_faces,v_faces):
    """ Returns the cube faces orientation after a single CCW spin action; Only h_faces are affected
        It applies a face shiftof these faces, and updates the F face on the v_faces dict."""
    
    global dbl                              # global dbl is used
    h_faces['L']=h_faces['F']               # CCW face shift
    h_faces['F']=h_faces['R']               # CCW face shift
    h_faces['R']=opp_face(h_faces['L'])     # CCW face shift, via opposite face
    v_faces['F']=h_faces['F']               # CCW face shift
    dbl = spinCCW_dbl(dbl)                  # dbl cubie location is updated
       





def spinCCW_dbl(dbl):
    """ Returns the dbl cubie position after a CCW rotation."""
    
    if dbl==1 or dbl==5:                    # case dbl cubie is at 1 or 5
        dbl += 1                            # cubie is shifted by +1
    elif dbl==2 or dbl==6:                  # case dbl cubie is at 2 or 6
        dbl += 2                            # cubie is shifted by +2
    elif dbl==3 or dbl==7:                  # case dbl cubie is at 3 or 7
        dbl -= 2                            # cubie is shifted by -2
    elif dbl==4 or dbl==8:                  # case dbl cubie is at 4 or 8
        dbl -= 1                            # cubie is shifted by -1
    return dbl                              # shifted dbl cubie is returned





def spinCW_effect(h_faces,v_faces):
    """ Returns the cube faces orientation after a single CW spin action; Only h_faces are affected
        It applies a face shiftof these faces, and updates the F face on the v_faces dict."""
    
    global dbl                              # global dbl is used
    h_faces['R']=h_faces['F']               # CW face shift
    h_faces['F']=h_faces['L']               # CW face shift
    h_faces['L']=opp_face(h_faces['R'])     # CW face shift, via opposite face
    v_faces['F']=h_faces['F']               # CW face shift
    dbl = spinCW_dbl(dbl)                   # dbl cubie location is updated
    






def spinCW_dbl(dbl):
    """ Returns the dbl cubie position after a CW rotation."""
    
    if dbl==1 or dbl==5:                    # case dbl cubie is at 1 or 5
        dbl += 2                            # cubie is shifted by +2
    elif dbl==2 or dbl==6:                  # case dbl cubie is at 2 or 6
        dbl -= 1                            # cubie is shifted by -1
    elif dbl==3 or dbl==7:                  # case dbl cubie is at 3 or 7
        dbl += 1                            # cubie is shifted by +1
    elif dbl==4 or dbl==8:                  # case dbl cubie is at 4 or 8
        dbl -= 2                            # cubie is shifted by -2
    return dbl                              # shifted dbl cubie is returned








def cube_orient_update(movement):
    """ This function traks the cube orientation based on the applied movements by the robot.
        Arguments is the applied robot movement.
        The function uses the cube orientation global variables  "h_faces" and "v_faces"."""
        
    global h_faces,v_faces
    
    for i in range(len(movement)):                 # iterates over the string of robot movements
        if movement[i] == 'F':                     # case there is a cube flip on robot movements
            repeats=int(movement[i+1])             # retrieves how many flips
            for j in range(repeats):               # iterates over the amount of flip
                flip_effect(h_faces,v_faces)       # re-order the cube orientation on the robot due to the flip
        
        elif movement[i] == 'S':                   # case there is a cube spin on robot movements
            repeats=int(movement[i+1])             # retrieves how many spin
            if repeats==3:                         # case the spin is CCW
                spinCCW_effect(h_faces,v_faces)    # re-order the cube orientation on the robot due to the CCW spin
            else:                                  # case the spin is CW
                for j in range(repeats):           # iterates over the amount of spin
                    spinCW_effect(h_faces,v_faces) # re-order the cube orientation on the robot due to the CW spin             






def adapt_move(move):
    """ This function adapts the robot move after verifying on wich side the related face is located.
        The solver considers the cube orientation to don't change, but on the robot it does.
        This function will then swap the face name, instead to move the cube back on the original position
        The function returns a dict with all the robot moves and the total amount."""
    
    global h_faces,v_faces,dbl_move
    
    face_to_turn = move[0]                        # face to be turned according to the solver
    rotations = move[1]                           # rotations (string) to be applied according to the solver
        
    cube_orientation=h_faces.copy()               # generating a single cube orientation dict with h_faces
    cube_orientation.update(v_faces)              # generating a single cube orientation dict with h_faces and v_faces
    
    dbl_move = False
    if face_to_turn in ('D', 'B', 'L'):           # case the face_to_turn affects the DBL corner
        dbl_move = True                           # dbl_move variable is set True
        
    for side, face in cube_orientation.items():   # iteration over the current cube orientation dict (5 sides)
        if face == face_to_turn:                  # case the face to be turned is in the dictionary value
            return side+rotations, dbl_move       # the dictionary key is returned, as the effective face location
        else:                                     # case the face to be turned is not in the dictionary value
            solution_in_dict = False              # boolean variable is changed to False
    
    if solution_in_dict == False:                 # case the face to be turned is not in the dictionary value
        return 'B'+rotations, dbl_move            # the face to be turned must be the 6th one, the B side







def change_cube_orientation(robot_seq):
    """This function is called when the DBL corner gets rotated caused by a D B L face rotation.
    This is necessary to reflect the dbl rotation (CW or CCW) with reference to the adiacent layer.
    This function is not necessary on a 3x3x3 cube.
    As outcome, the complete 'cube' is reoriented on the tracked orientation.
    """
    
    global h_faces,v_faces,dbl
      
    for i in range(0,len(robot_seq),2):         # iteration over the robot movements
        move = robot_seq[i:i+2]                 # single ronot movement
        if 'R3'in move and dbl in (5,6,7,8):    # case the bottom layer is CCW rotated and dbl cubie on the bottom layer
            spinCCW_effect(h_faces,v_faces)     # update the orientation to the real cube position on the robot
        elif 'R1'in move and dbl in (5,6,7,8):  # case the bottom layer is CW rotated and dbl cubie on the bottom layer
            spinCW_effect(h_faces,v_faces)      # update the orientation to the real cube position on the robot







def optim_moves1(moves, informative):
    """Removes unnecessary moves that would cancel each other out, to reduce solving moves and time
    These movements are for instance a spin CW followed by a spin CCW, or viceversa."""
    
    printout = False
    
    if printout:
        print("initial moves: ", moves)
        print("len initial moves:", len(moves))
        
    optimization = False                 # boolean to track if optimizations are made
    to_optmize=[]                        # empty list to be populated with string index where optimization is possible
    str_length=len(moves)                # length of the robot move string
    idx=0                                # index variable, of optimizable move string locations, to populate the list
    for i in range(0,str_length,2):      # for loop of with steps = 2
        
        if moves[idx:idx+2]=='S1' and moves[idx+2:idx+4] =='S3':  # case S1 is folloved by S3
            if printout:
                print(f'S1 followed by S3 at index {idx}')
            optimization = True          # boolean to track optimization is set true
            to_optmize.append(idx)       # list is populated with the index 
            idx+=4                       # string index is increased by four, to skip the 2nd (already included) move  

        elif moves[idx:idx+2]=='S3'and moves[idx+2:idx+4] =='S1': # case S3 is folloved by S1
            if printout:
                print(f'S3 followed by S1 at index {idx}')
            optimization = True          # boolean to track optimization is set true
            to_optmize.append(idx)       # list is populated with the index 
            idx+=4                       # string index is increased by four, to skip the 2nd (already included) move  

        idx+=2                           # index variable is increased by two, to analayse next move
        if idx>=str_length+2:            # case the index variable reaches the string end 
            break                        # for loop is interrupted

    if optimization == False:            # case the moves string had no need to be optimized
        if printout:
            print("Robot moves string: not optimization type 1 needed")
            print("moves at opt1: ", moves)
            print("len moves at opt1:", len(moves))
        return moves, 0                  # original moves are returned

    else:                                # case the moves string has the need to be optimized
        to_remove=[]                     # empty list to be populated with all indididual characters to be removed from the moves
        for i in to_optmize:             # iteration over the list of moves to be optimized
            to_remove.append((i, i+1, i+2, i+3))   # list is populated with the 4 caracters of the 2 moves
        
        new_moves=''                     # empty string to hold the new robot moves 
        remove = [item for sublist in to_remove for item in sublist] # list of characters is flattened
        for i in range(str_length):      # iteration over all the characters of original moves
            if i not in remove:          # case the index is not included in the list of those to be skipped
                new_moves+=moves[i]      # the character is added to the new string of moves 
        
        if informative:
            print("Robot moves string: applied optimization type 1")
        
        if printout:
            print("new_moves at opt1: ", new_moves)
            print("len new_moves at opt1:", len(new_moves))
        return new_moves, 1              # the new string of robot moves is returned






def optim_moves2(moves, informative):
    """Removes 2 flips when the second-last flip is F3, the last one is F2 and both are followed by same spins/rotations.
        Under these conditions, the second-last flip (F3) can be changed (to F1)."""
    # the case for this optimization is never found on the 2x2x2 cube







def optim_moves3(moves, informative):
    """Removes 2 flips when the last flip is F3, as the same end result is achieved with a F1 instead."""
    
    printout = False
    
    F3_pos = -1                          # F3_pos variable is set to a negative integer
    str_length = len(moves)              # length of the robot move string                        
    for i in range(str_length-2,-2,-2):  # iteration over the moves string, from the end, in steps of 2
        if moves[i] == 'F':              # case there is a F (flip) into the moves string
            if moves[i+1] == '3':        # case the last 'F' is followed by '3'
                F3_pos = i               # F3_pos gets the (last F3) position in string
                break                    # for loop is interrupted
            else:                        # case the last 'F' is not followed by '3'
                return moves, 0          # moves in argument are returned
                
    if F3_pos >= 0:                      # case F3_pos got assigned an index do a string position for 'F3'
        new_moves=''                     # new_moves empty string to be populated with the new moves
        for i in range(str_length):      # iteration over the moves string
            if i == F3_pos+1:            # moves index where to apply the change, from 3 (F3) to 1 (F1)
                new_moves += '1'         # character 1 is added to the new_moves string
            else:                        # moves index to keep the original moves
                new_moves += moves[i]    # original moves charactes are appended to new_moves string
        
        if informative:
            print("Robot moves string: applied optimization type 3")
        
        if printout:
            print("new_moves at opt3: ", new_moves)
            print("len new_moves at opt3:", len(new_moves))
        return new_moves, 1              # the new string of robot moves is returned
        
    else:                                # case no one 'F' in string
        return moves, 0                  # moves in argument are returned







def count_moves(moves):
    """Counts the total amount of robot movements."""

    robot_tot_moves = 0               # counter for all the robot movements
    for i in range(len(moves)):       # iterates over the string of robot movements
        if moves[i] == 'F':           # case there is a cube flip on robot movements
            flips=int(moves[i+1])     # retrieves how many flips
            robot_tot_moves+=flips    # increases the total amount of robot movements
        elif moves[i] == 'R':         # case there is a layer rotation on robot movements
            robot_tot_moves+=1        # increases by 1 (cannot be more) the total amount of robot movements
        elif moves[i] == 'S':         # case there is a cube spin on robot movements
            robot_tot_moves+=1        # increases by 1 (cannot be more) the total amount of robot movements
    return robot_tot_moves            # total amount of robot moves is returned



    


def alt_solutions(solution):
    """ This function generates alternative solutions (cube face rotations), by including the D B L faces rotations."""
    
    if len(solution)>2:
        solutions = [solution]
        sol = solution[:2]
        sol_0 = solution[2:]
        sol_1 = sol_0
        sol_2 = sol_0
        sol_3 = sol_0
        sol_4 = sol_0
        sol_5 = sol_0
        sol_6 = sol_0
        
        if 'U' in sol_1:
            solutions.append(sol + sol_1.replace('U', 'D'))
        if 'R' in sol_2:
            solutions.append(sol + sol_2.replace('R', 'L'))
        if 'F' in sol_3:
            solutions.append(sol + sol_3.replace('F', 'B'))
        if 'U' in sol_4 and 'R' in sol_4:
            solutions.append(sol + sol_4.replace('U', 'D').replace('R', 'L'))
        if 'U' in sol_5 and 'F' in sol_5: 
            solutions.append(sol + sol_5.replace('U', 'D').replace('F', 'B'))
        if 'R' in sol_6 and 'F' in sol_6:
            solutions.append(sol + sol_6.replace('R', 'L').replace('F', 'B'))
        return solutions
    
    else:
        return solution







def robot_required_moves(solution, solution_Text, simulation, informative=False):
    """ This function splits the cube manouvre from Kociemba solver string, and generates a dict with all the robot movements.
        Based on the dict with all the robot moves, a string with all the movements is generated.
        The string with the robot movements might differ from the dict, when optimizing is possible."""
    
    global h_faces,v_faces,dbl,dbl_move
    
    solution=solution.strip()                     # eventual empty spaces are removed from the string
    solution=solution.replace(" ", "")            # eventual empty spaces are removed from the string
    starting_cube_orientation(simulation)         # Cube orientation at the start, later updated after every cube movement on the robot
    robot={}                                      # empty dict to store all the robot moves
    moves=''                                      # empty string to store all the robot moves
    robot_tot_moves = 0                           # counter for all the robot movements
    
    if solution_Text != 'Error':                  # case the solver did not return an error
        blocks = int(round(len(solution)/2,0))    # total amount of blocks of movements (i.e. U2R1L3 are 3 blocks: U2, R1 and L1)
        
        # cube orientation and robot movement sequence selection
        for block in range(blocks):               # iteration over blocks of movements
            move=solution[:2]                     # move to be applied on this block, according to the solver
            solution=solution[2:]                 # remaining movements from the solver are updated
            adapted_move, dbl_move = adapt_move(move)   # the move from solver is adapted considering the real cube orientation
            robot_seq=moves_dict[adapted_move]    # robot movement sequence is retrieved
            robot[block]=robot_seq                # robot movements dict is updated
            moves+=robot_seq                      # robot movements string is updated
            cube_orient_update(robot_seq)         # cube orientation updated after the robot move from this block
            
            if dbl_move:                          # case the DBL corner has been rotated at least once (wrt other layers )
                change_cube_orientation(robot_seq)  # the cube orientation is adapted
        
        moves, opt1 = optim_moves1(moves, informative)  # removes eventual unnecessary moves (that would cancel each other out)
        moves, opt3 = optim_moves3(moves, informative)  # removes eventual unnecessary flips
        robot_tot_moves = count_moves(moves)      # counter for the total amount of robot movements
        opt = (opt1, opt3)                        # tuple indicating if the optimizers have been effective
    
    else:                                         # case the solver returned an error
        opt = (0,0)                               # tuple indicating the optimizers has not been effective
    
    
    # info:
    # "robot" variable (dict type) has all the robot movements prio the optimization analysis
    # "moves" variable (string typ) likely differs from the dict content due to optimized moves
    # "opt" tuple indicates if the optimezers (and positonally which one) could reduce the robot moves
    return robot, moves, robot_tot_moves, opt # returns a dict with all the robot moves, string with all the moves and total robot movements
    








if __name__ == "__main__":
    """ This function convert the cube solution string 'U2 L1 R1 D2 B2 R1 D2 B2 D2 L3 B3 R3 F2 D3 L1 U2 F2 D3 B3 D1' in robot moves
        Robot moves are printed on the REPL
        Robot moves are translated to servo moves: Initially are print per ach of the cube solving string manoeuvre
        Afterward all the strings are combined in a single string, for the Cubotino_servo.py module to control the servos."""  
    
    
#     solution = 'U3 R3 F3 U3 F3'     # this cube solution allows type 3 optimization (2 flips removal)
    solution = 'F3R3U3'

    print()
    print("Example of robot movements for solver solution: ", solution)
    print("Robot moves are noted with the 3 letters S, F, R (Spin, Flip, Rotate) followed by a number")
    print("Number '1' for S ans R identifies CW rotation, by loking to the bottom face, while number '3' stands for CCW")
    print("Example 'F1R1S3' means: 1x cube Flip, 1x (90deg) CW rotation of the 1st (bottom) layer, 1x (90deg) CCW cube Spin")
    print()
    
    
    solutions = alt_solutions(solution)
    print("\nPossible alternative solutions:", solutions)
            
    for solution in solutions:
        print(f'\nSolution: {solution}')
        solution_Text = ""
        robot, moves, robot_tot_moves, opt = robot_required_moves(solution, solution_Text, informative=False, simulation=False)
        print(f'Number of robot movements: {robot_tot_moves}')
        print(f'Robot movements: ')
        servo_moves=""
        for step, movements in robot.items():
            print(f'step:{step}, robot moves:{movements}')
            servo_moves+=moves
        print(f'String command to the robot servos driver: {moves}\n')
